qtxs/head-md-future-of-drawing/process/main/2023-12-12/readme.md

# Planning

12.12.2023

Plan for the day

1. Book atelier metal for the first week after vacation
2. Talk with Pierre about project, about 3d print 
3. Prepare for Test Day:

- Read doc again
- Make prototypes
- User scenario
- Better poetry definition
- ...
