qtxs/head-md-future-of-drawing/process/main/2023-12-20/readme.md

# Prototying

In this folder you can find the current version of my assistant, made with two parts.

Things to define:

- final final dimensions
- the small box opening system

I struggle with this two points becase I need my electronics to understand it entirely. All dimensions and sizes in my model are approximativ but very close to reality.

I could find some references for connecting my electronics together:

[!Reference Image](/process/prototyping/2023-12-20/20231912_Connections01.png/)
[!Reference Image](/process/prototyping/2023-12-20/20231912_Connections02.png/)

The entire wiring system shoulb be looking like so:

[!Reference Image](/process/prototyping/2023-12-20/20231912_Wiring.pdf)

Basically in REAL life project, it should be conecting two parts by bluetooth, but for demo I will connect it by cables.

Theses were the sletches:

[!Reference Image](/process/prototyping/2023-12-20/20231912_Sketches01.png)
[!Reference Image](/process/prototyping/2023-12-20/20231912_Sketches02.png)
[!Reference Image](/process/prototyping/2023-12-20/20231912_Sketches03.png)
[!Reference Image](/process/prototyping/2023-12-20/20231912_Sketches04.png)
[!Reference Image](/process/prototyping/2023-12-20/20231912_Sketches05.png)

Yet after discussion with Laure, it came out that this type of object is no more relevant and it requires major changes. (see next day)
