qtxs/head-md-future-of-drawing/process/main/2023-10-30/20231030_Prototype_01.2.JPG

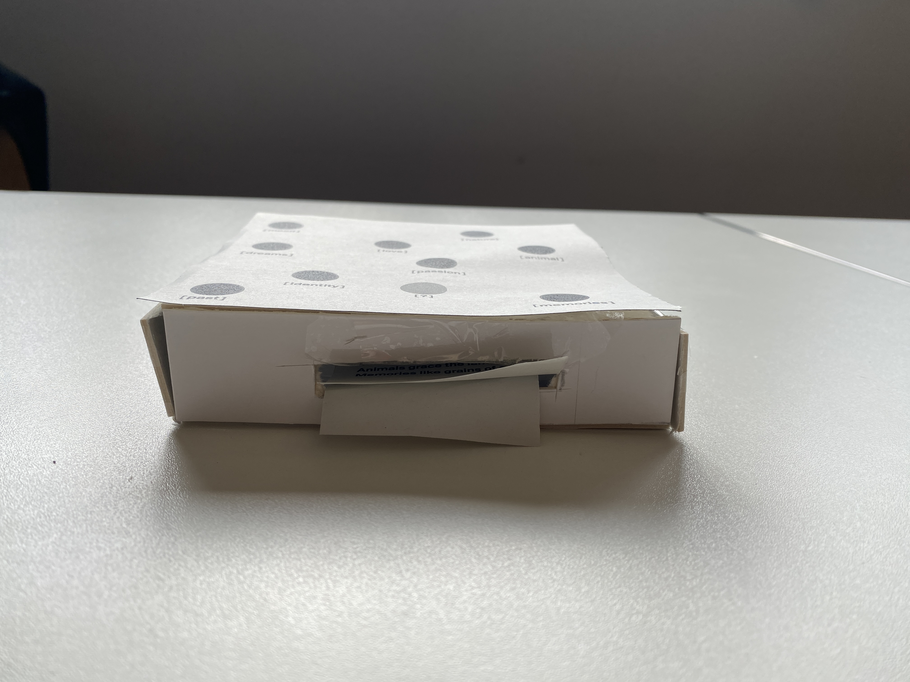
process/main/2023-10-30/20231030_Prototype_01.2.JPG
