qtxs/head-md-future-of-drawing/process/main/2023-11-02/20231103_Idea02_User_Journey.png

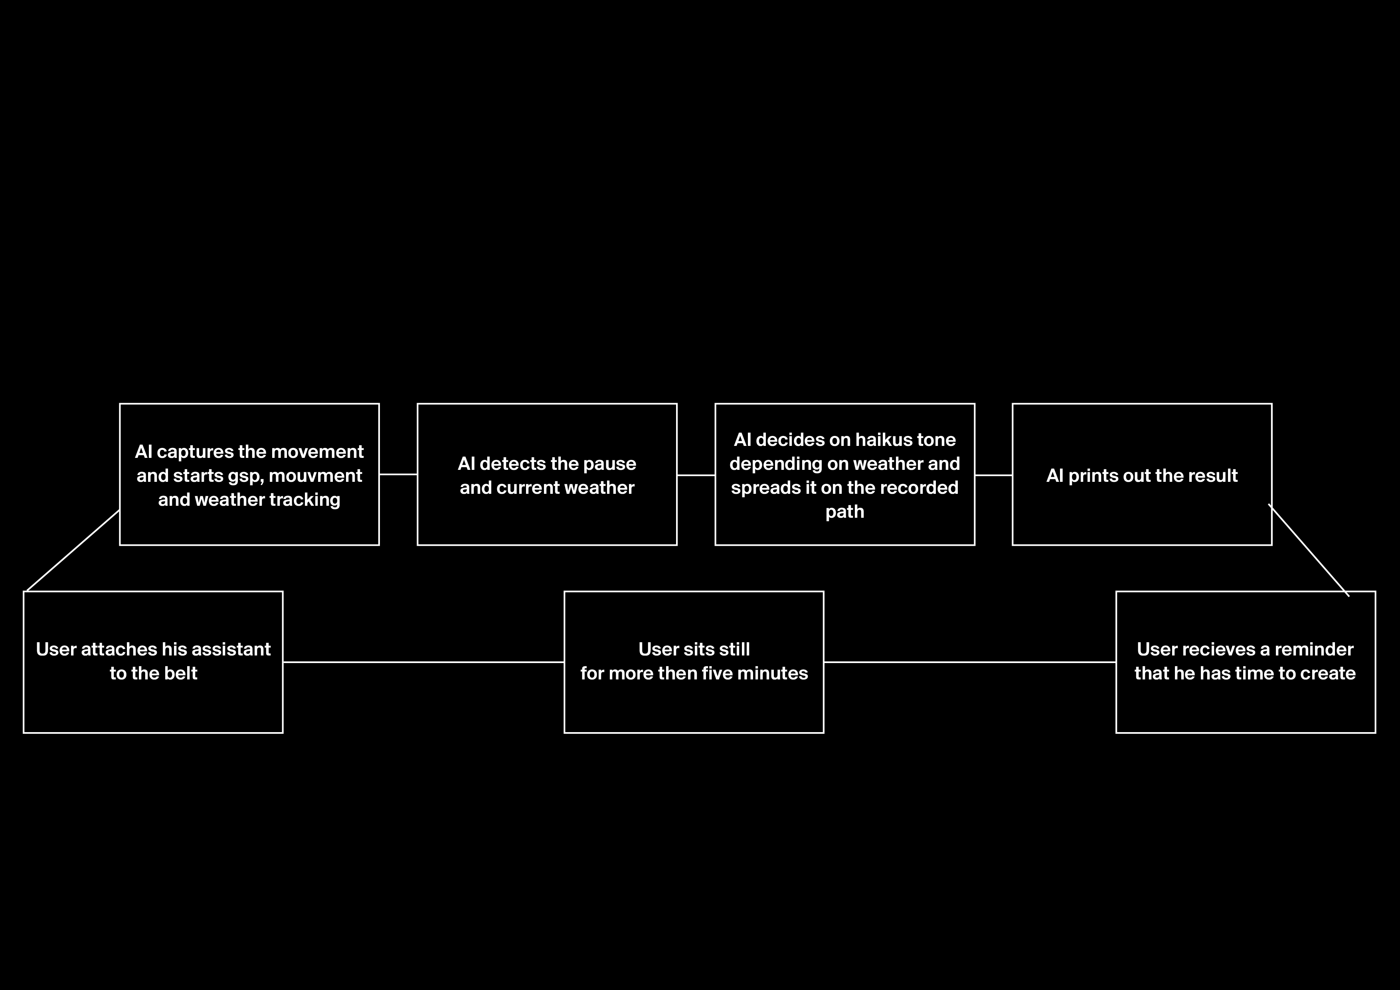
process/main/2023-11-02/20231103_Idea02_User_Journey.png
