qtxs/head-md-future-of-drawing/process/main/2023-11-16/20231116_MyBox02.png

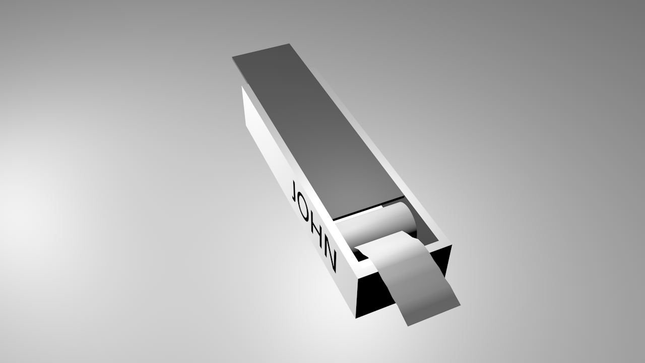
process/main/2023-11-16/20231116_MyBox02.png
