qtxs/head-md-future-of-drawing/process/main/2023-11-16/20231116_RefBox03.png

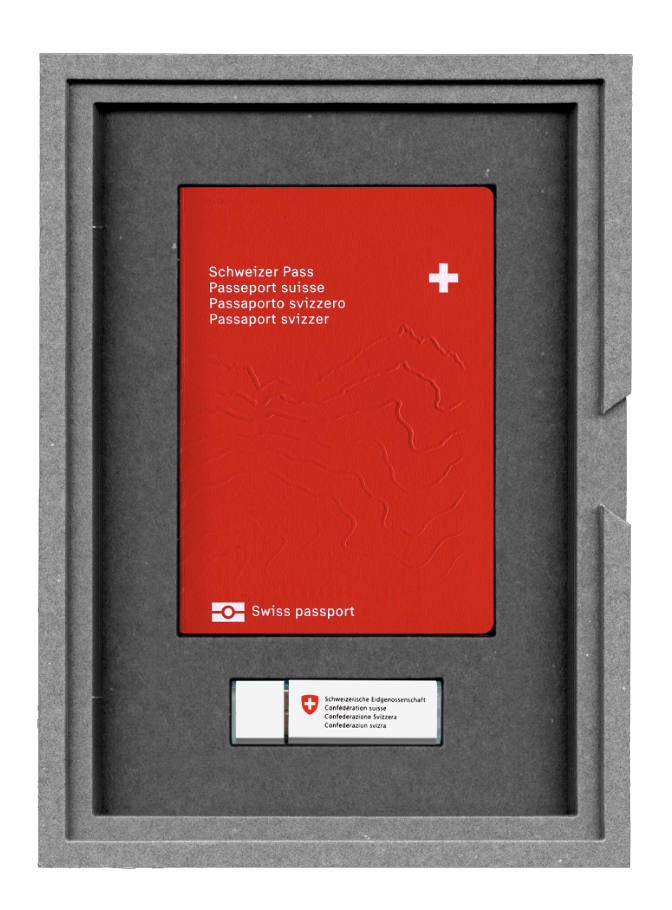
process/main/2023-11-16/20231116_RefBox03.png
