qtxs/head-md-future-of-drawing/process/main/2023-11-23/20231121_Ref01.jpeg

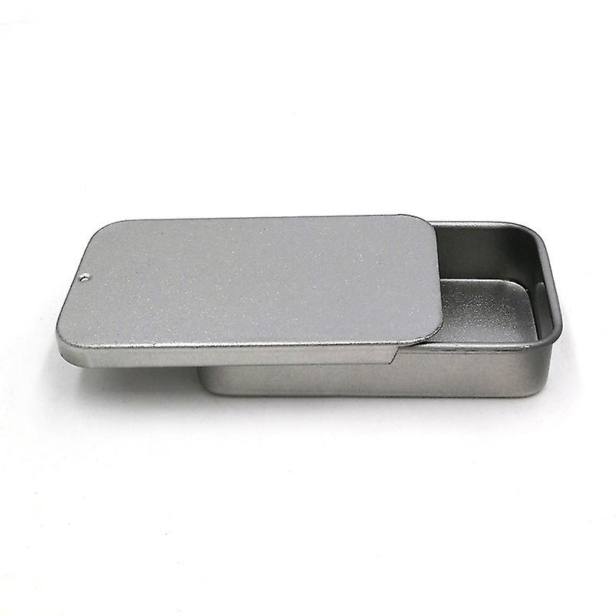
process/main/2023-11-23/20231121_Ref01.jpeg
