qtxs/head-md-future-of-drawing/process/main/2023-12-04/20231204_Ref02.png

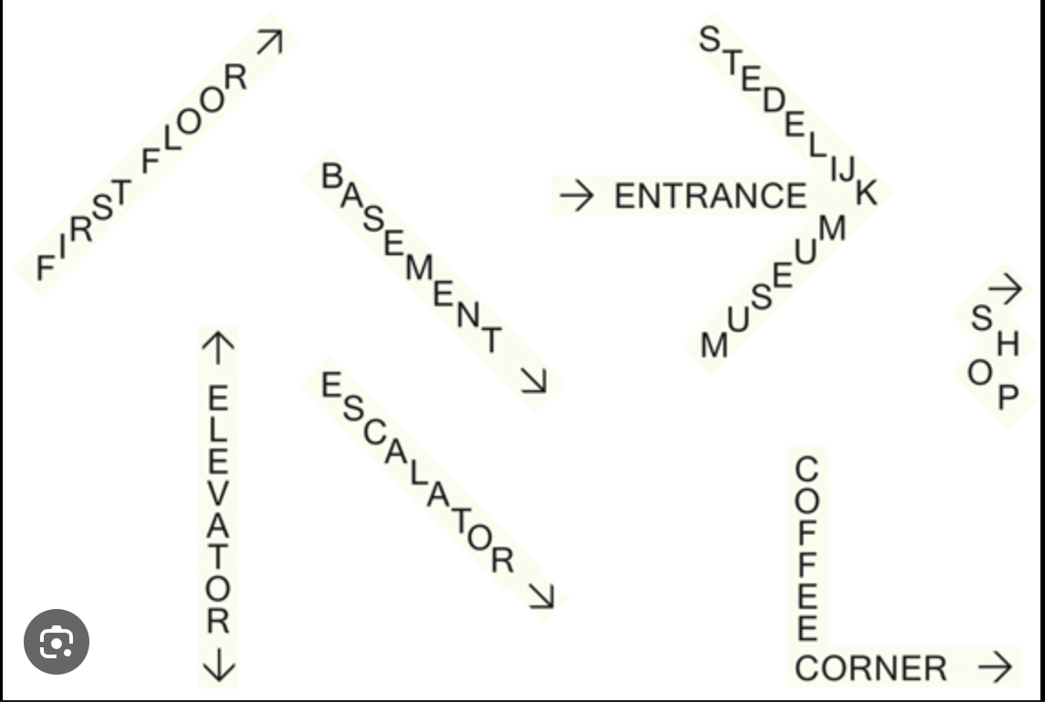
process/main/2023-12-04/20231204_Ref02.png
