qtxs/head-md-future-of-drawing/process/main/2023-12-08/20231208_Boxes2.png

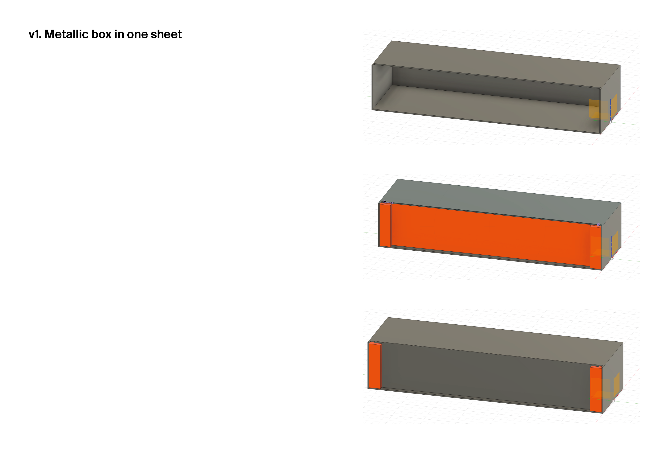
process/main/2023-12-08/20231208_Boxes2.png
