qtxs/head-md-future-of-drawing/process/main/2023-12-20/20231912_Sketches03.png

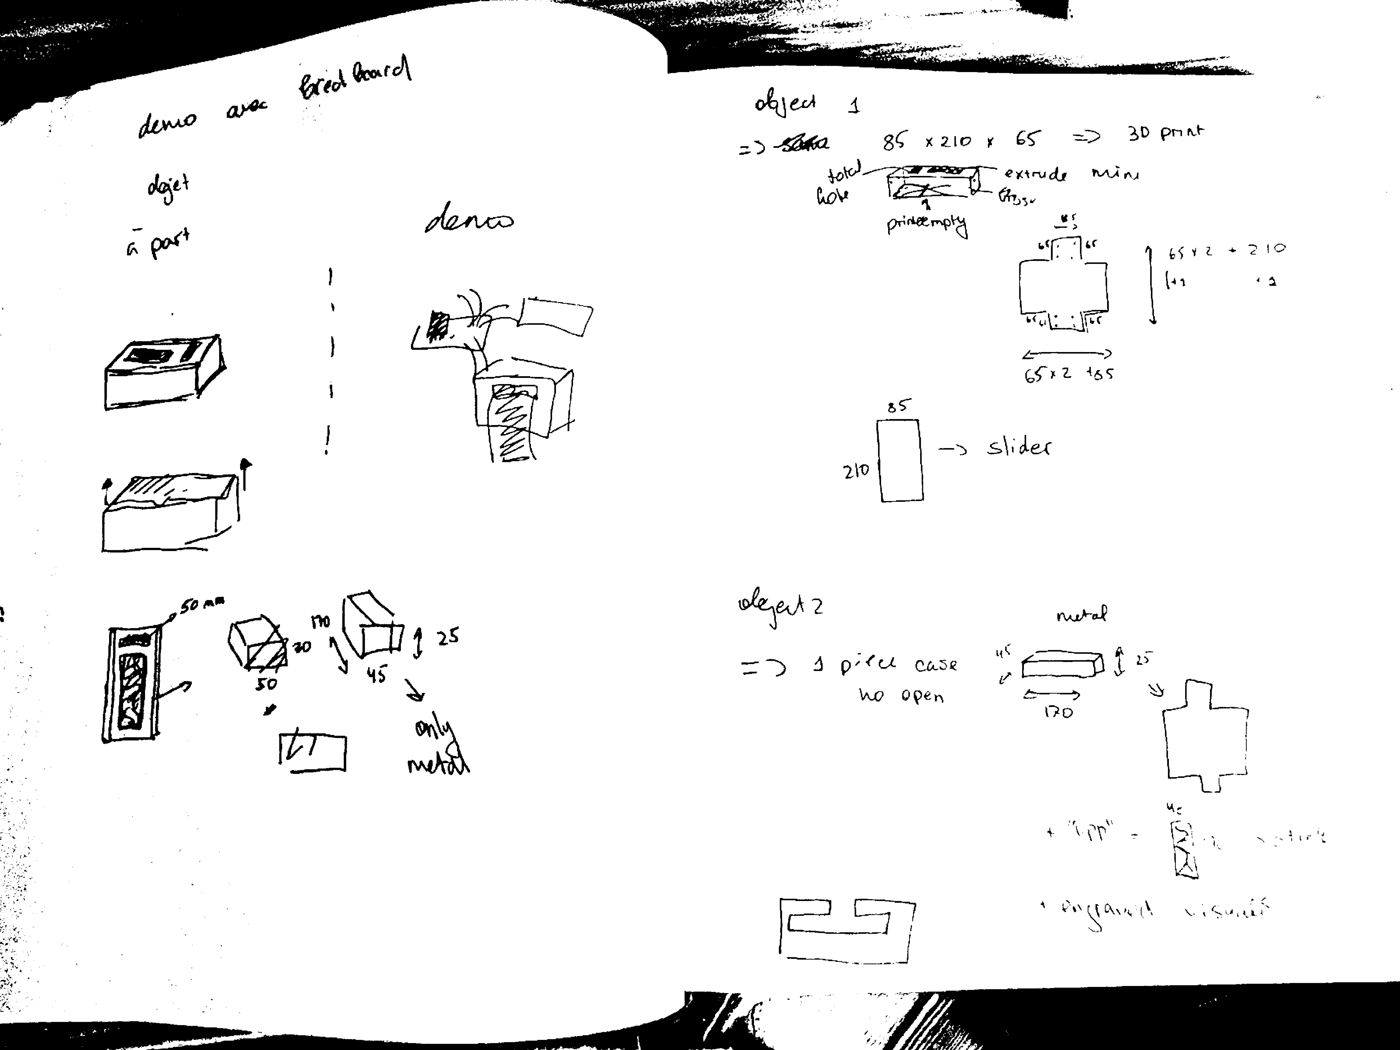
process/main/2023-12-20/20231912_Sketches03.png
