qtxs/head-md-future-of-drawing/process/main/2023-12-21/20231221_NewRefs/image (5).png

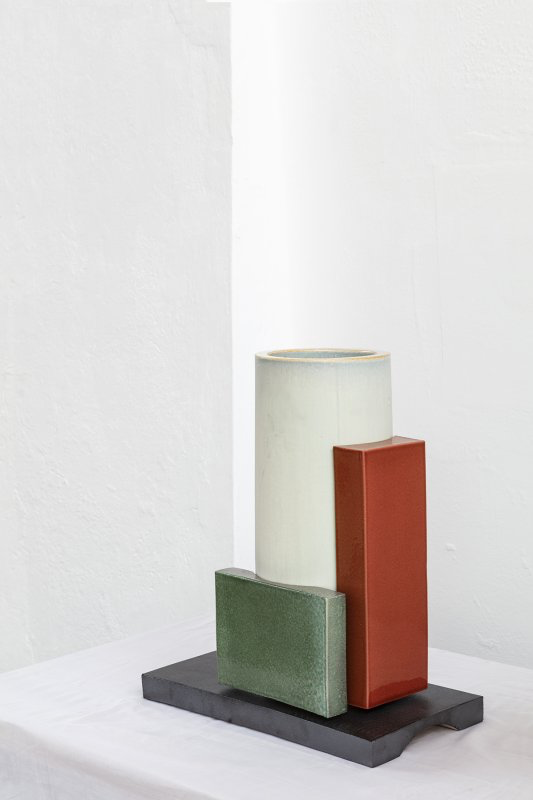
process/main/2023-12-21/20231221_NewRefs/image (5).png
