qtxs/head-md-future-of-drawing/process/main/2023-12-21/20231221_NewRefs/Screenshot 2023-12-21 at 11.53.56.png

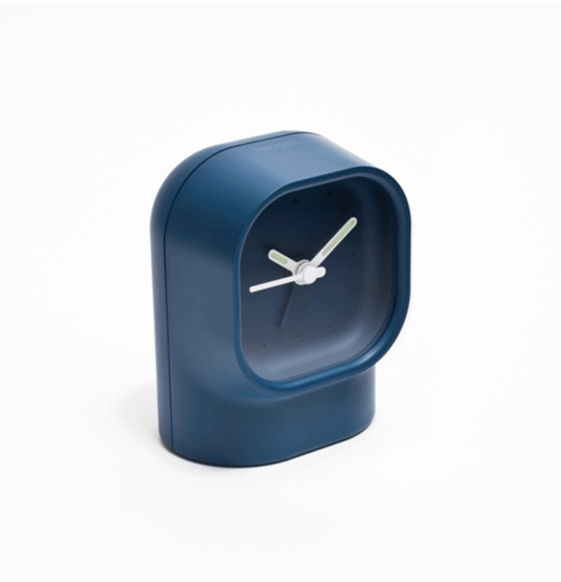
process/main/2023-12-21/20231221_NewRefs/Screenshot 2023-12-21 at 11.53.56.png
