qtxs/head-md-future-of-drawing/process/main/2023-12-29/20231229_Scheme02.png

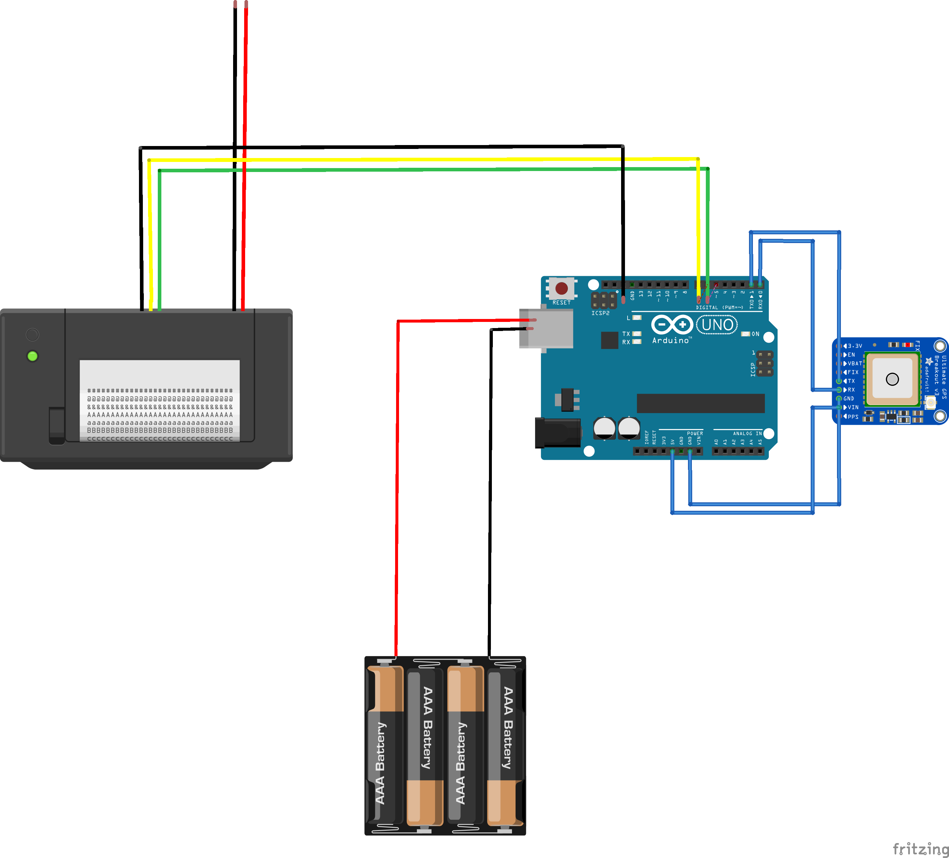
process/main/2023-12-29/20231229_Scheme02.png
