qtxs/head-md-future-of-drawing/process/main/2023-12-29/IMG_7831.JPG

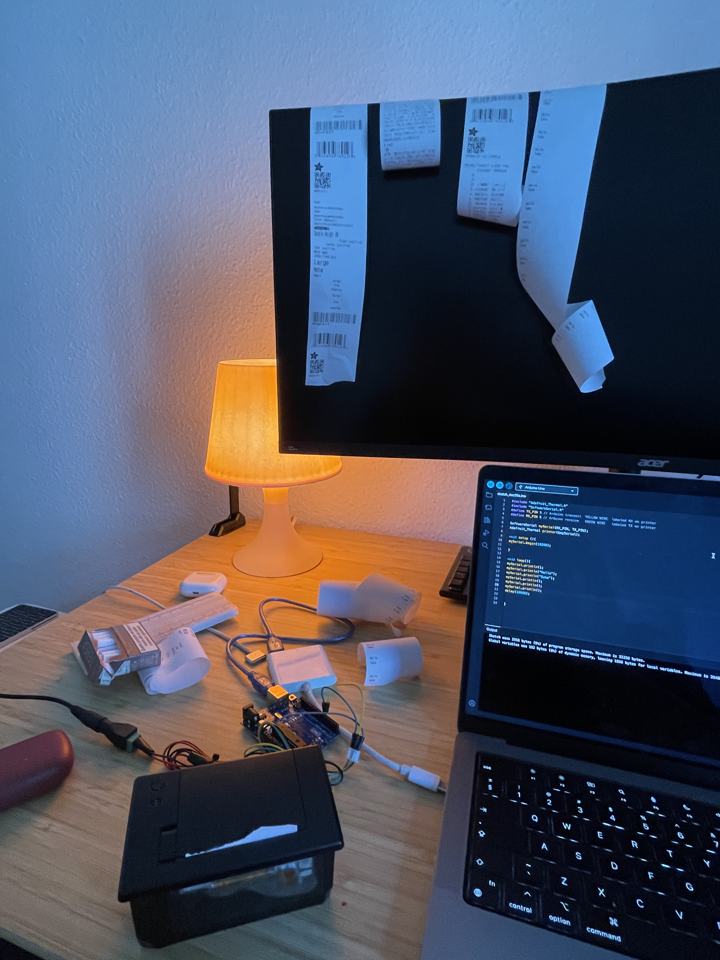
process/main/2023-12-29/IMG_7831.JPG
