qtxs/head-md-future-of-drawing/process/main/2024-01-05/Screenshot 2024-01-05 at 10.59.29.png

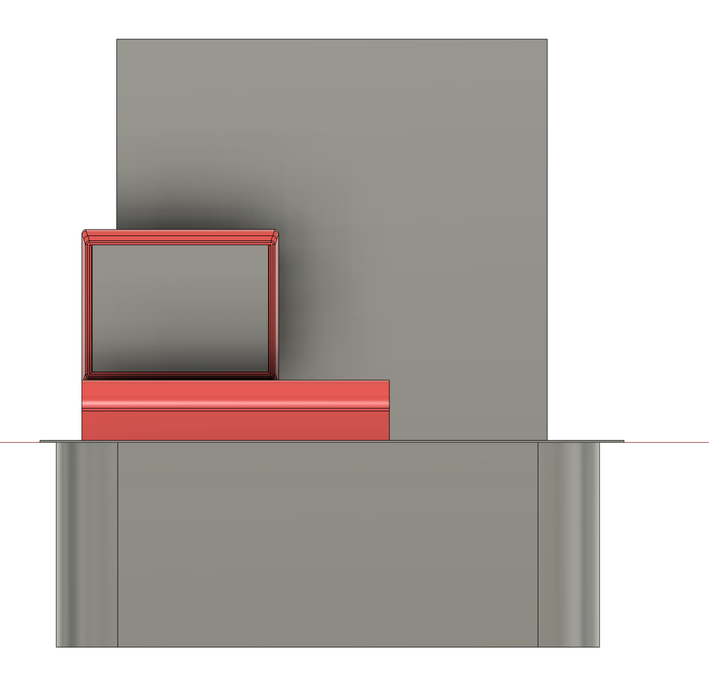
process/main/2024-01-05/Screenshot 2024-01-05 at 10.59.29.png
