qtxs/head-md-future-of-drawing/process/main/2024-01-10/20241210_Him.JPG

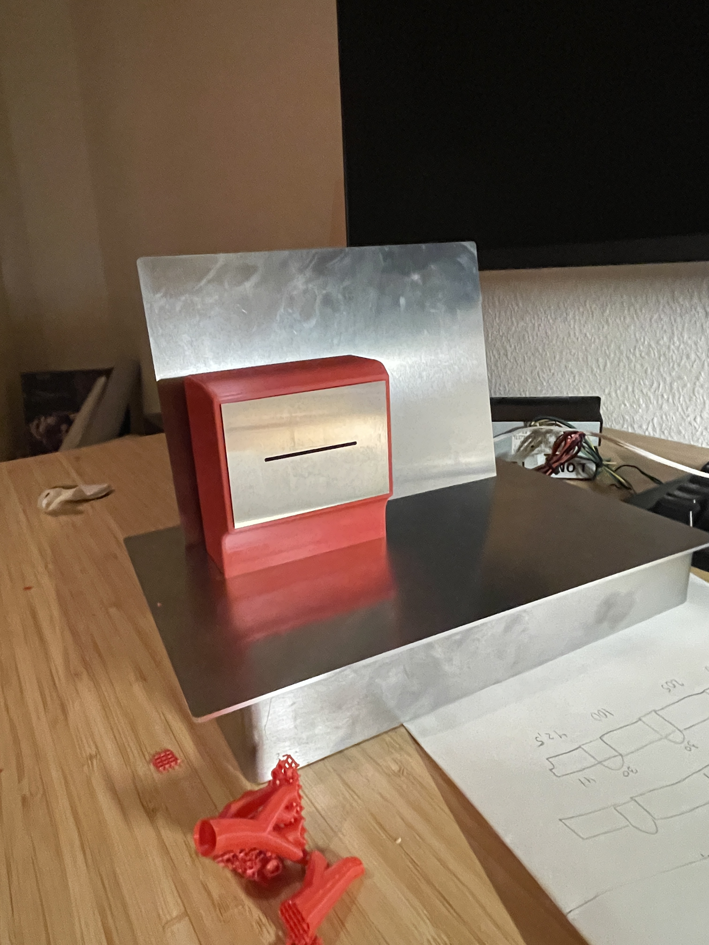
process/main/2024-01-10/20241210_Him.JPG
