qtxs/head-md-future-of-drawing/process/main/2024-01-10/20241210_ShapeNew.png

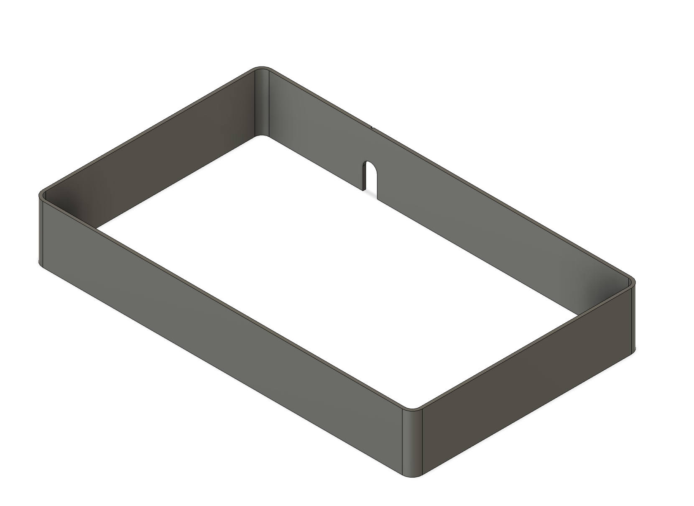
process/main/2024-01-10/20241210_ShapeNew.png
