qtxs/head-md-future-of-drawing/process/main/2024-01-10/20241210_Supports1.png

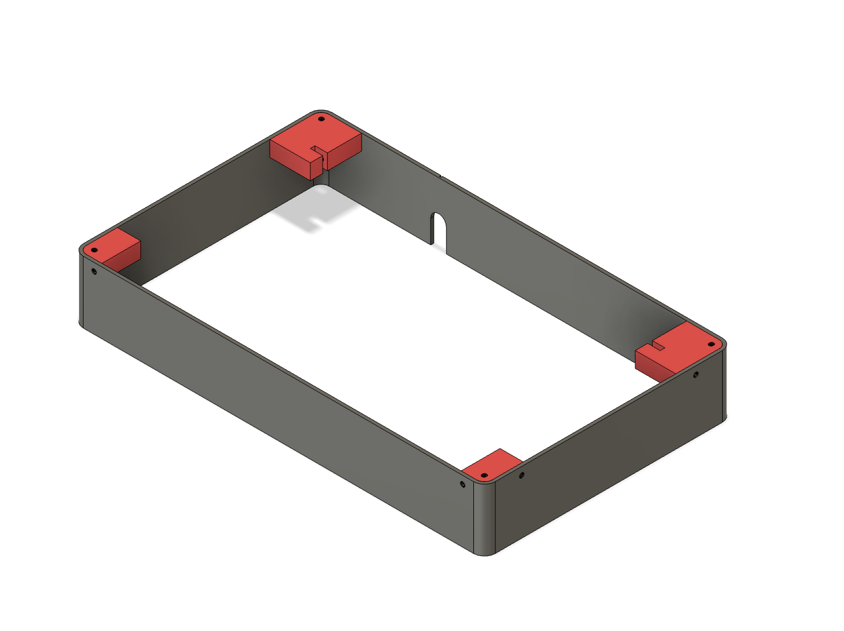
process/main/2024-01-10/20241210_Supports1.png
