qtxs/head-md-future-of-drawing/process/main/2024-01-12/20241212_Portable.png

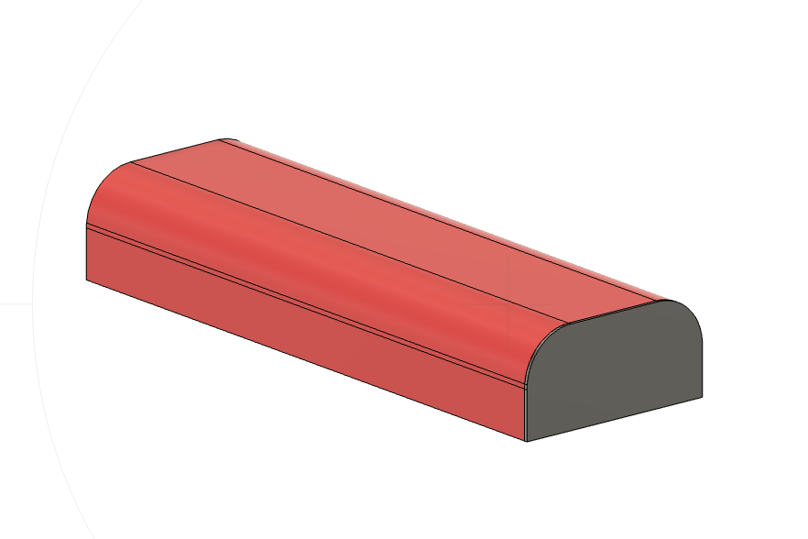
process/main/2024-01-12/20241212_Portable.png
