qtxs/head-md-future-of-drawing/process/main/2024-01-13/20240113_Solution0.png

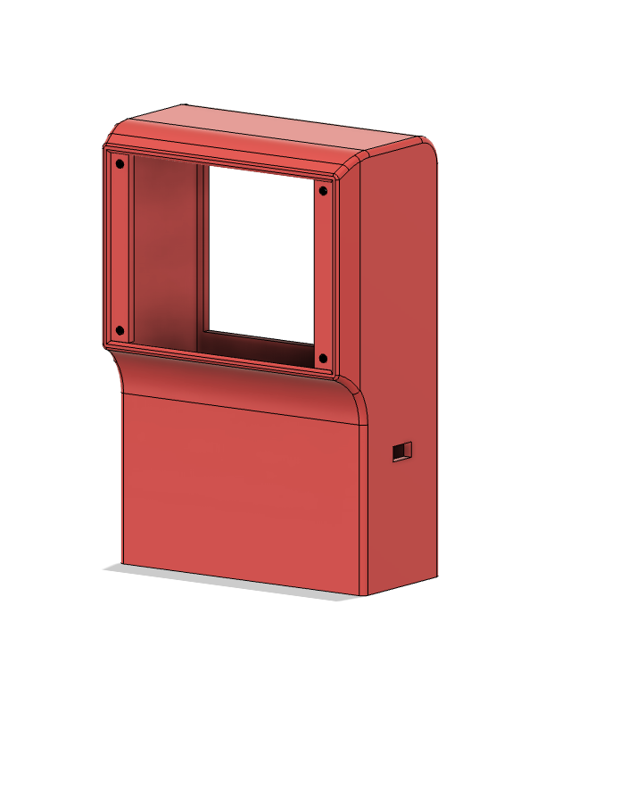
process/main/2024-01-13/20240113_Solution0.png
