qtxs/head-md-future-of-drawing/process/main/2024-01-15/Bitmaps/poems/poems4.png

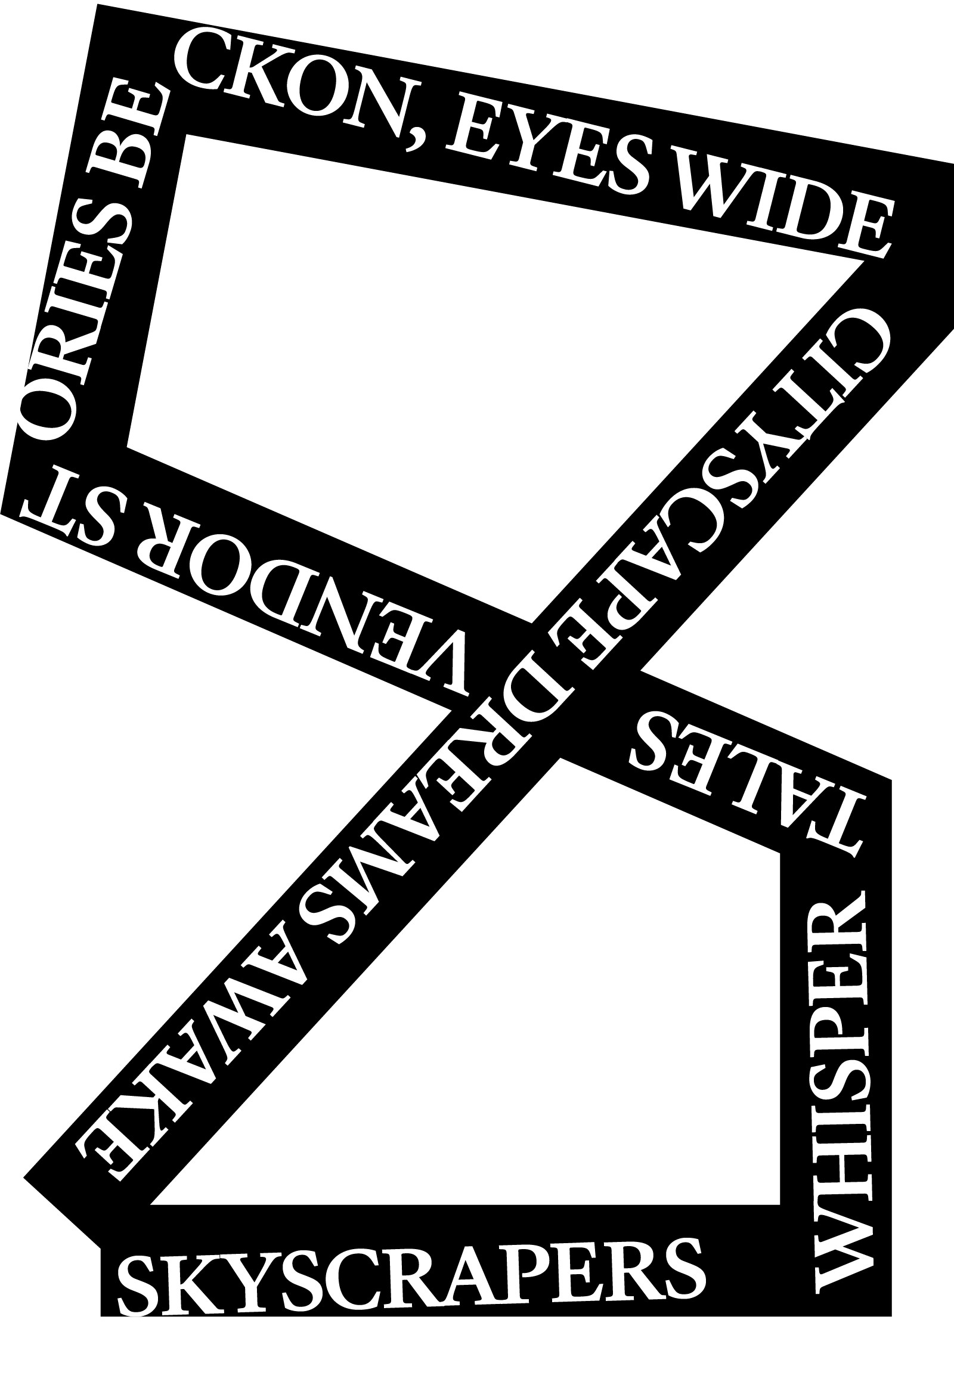
process/main/2024-01-15/Bitmaps/poems/poems4.png
