qtxs/head-md-future-of-drawing/process/main/2024-01-15/Bitmaps/scans/scan_ekaterin.bliznyuk_2024-01-15-14-48-56_1.jpeg

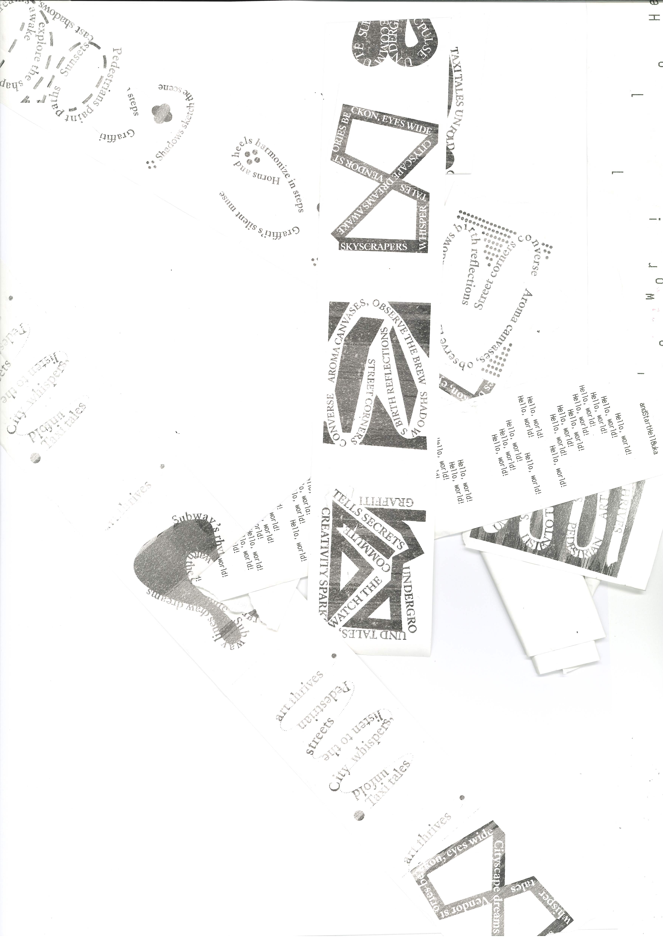
process/main/2024-01-15/Bitmaps/scans/scan_ekaterin.bliznyuk_2024-01-15-14-48-56_1.jpeg
