qtxs/head-md-future-of-drawing/process/main/2024-01-15/front01.png

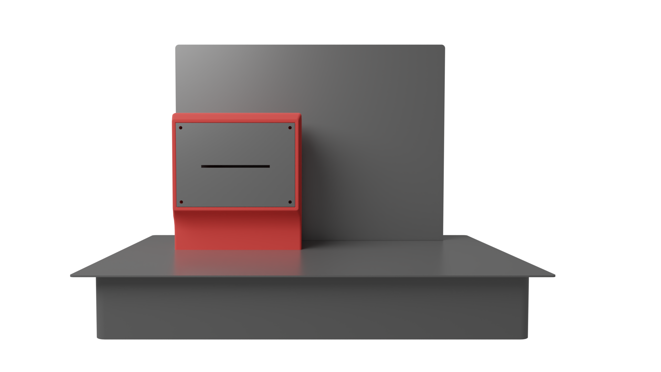
process/main/2024-01-15/front01.png
