qtxs/head-md-future-of-drawing/process/main/2024-01-16/20240116_CoverFront.png

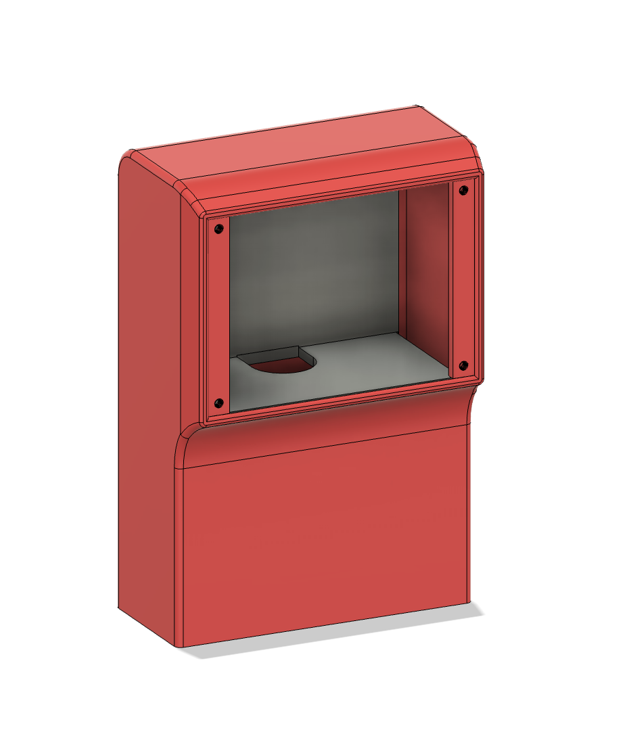
process/main/2024-01-16/20240116_CoverFront.png
