qtxs/head-md-future-of-drawing/process/main/2024-01-16/20240116_Nerding.JPG

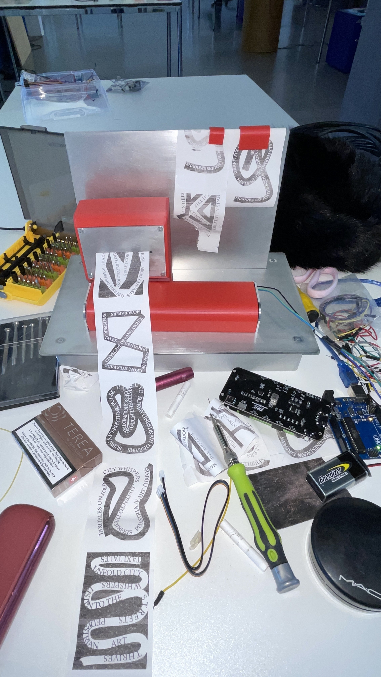
process/main/2024-01-16/20240116_Nerding.JPG
