qtxs/head-md-future-of-drawing/process/presentations/pres pics/IMG_7099.PNG

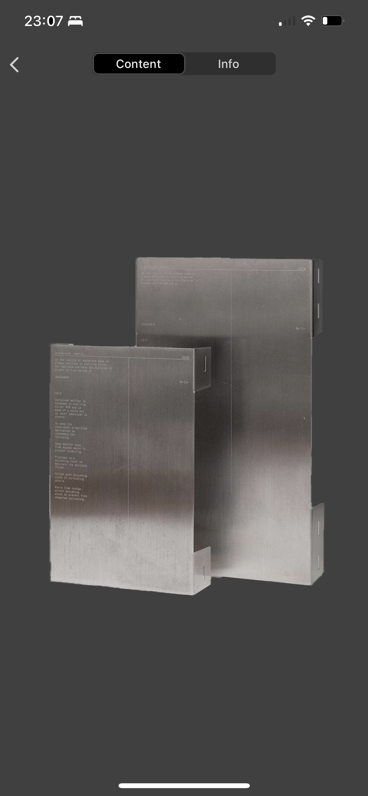
process/presentations/pres pics/IMG_7099.PNG
