qtxs/head-md-future-of-drawing/process/presentations/pres pics/IMG_7113.JPG

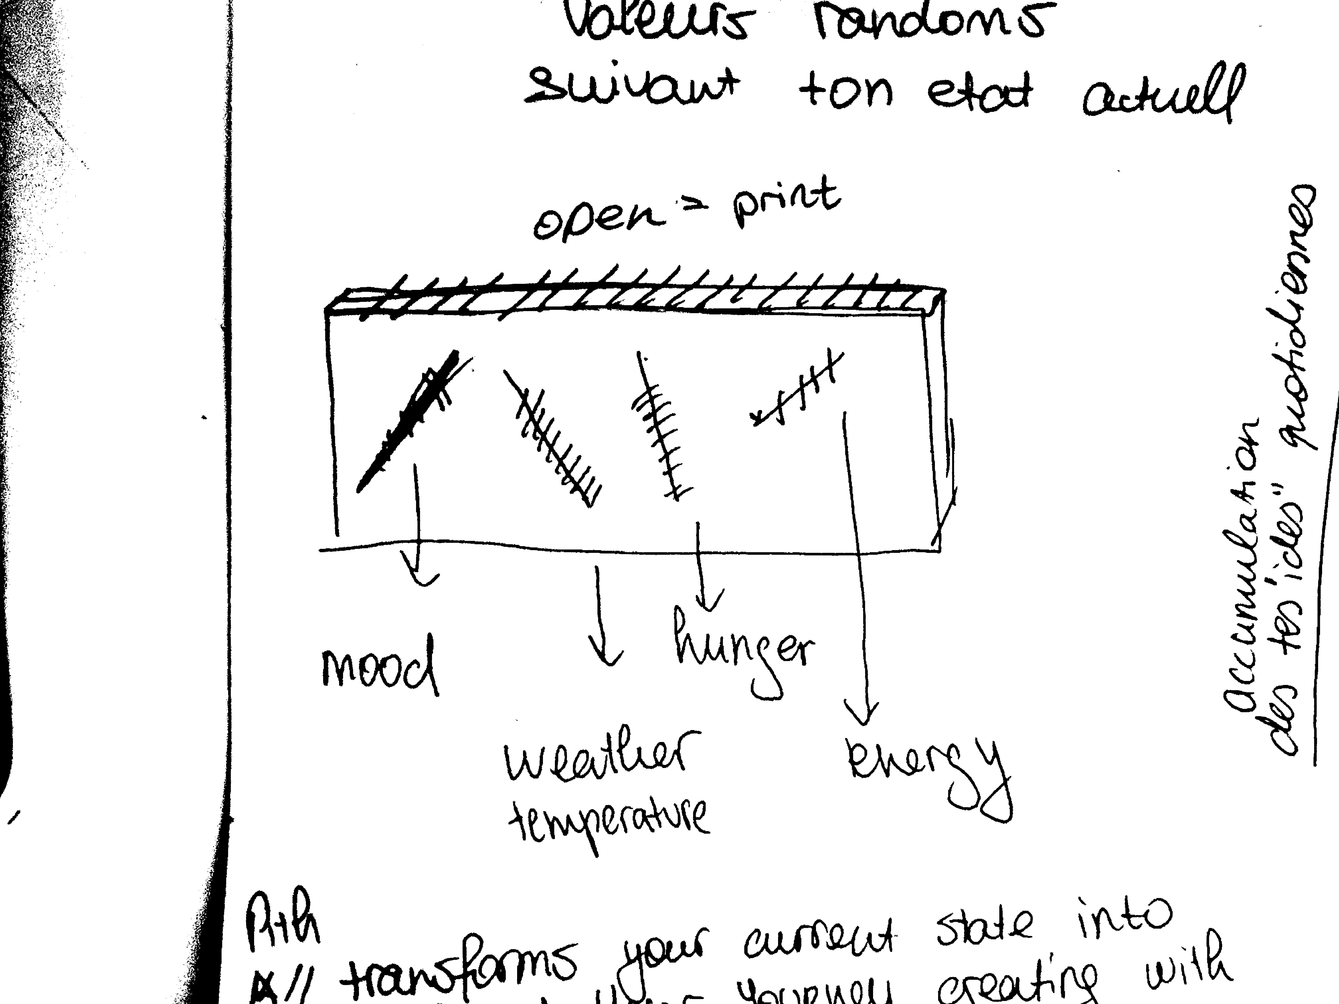
process/presentations/pres pics/IMG_7113.JPG
