qtxs/head-md-future-of-drawing/process/presentations/pres pics/IMG_7124.JPG

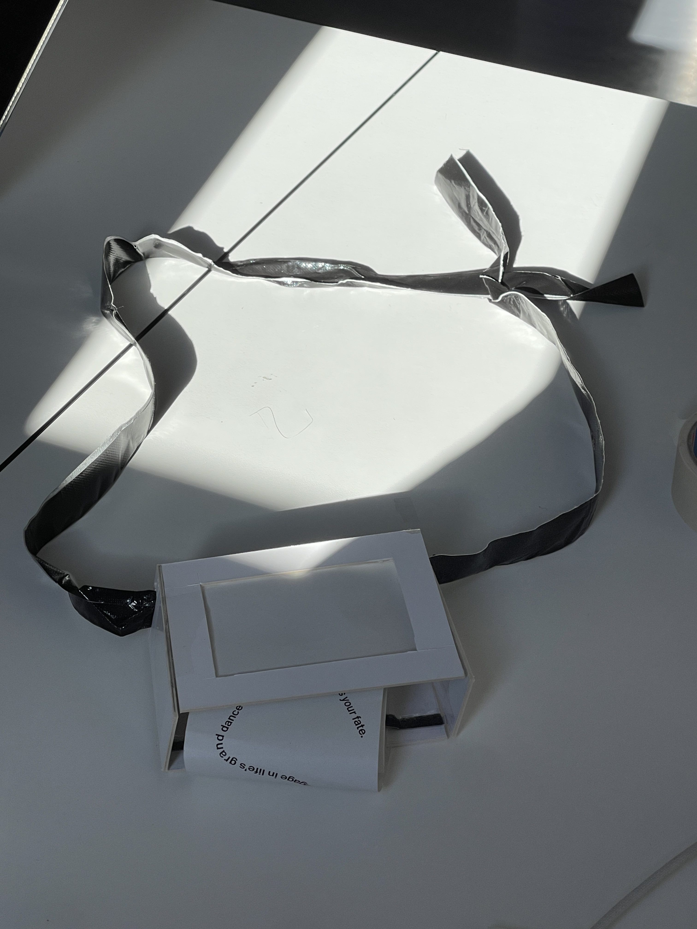
process/presentations/pres pics/IMG_7124.JPG
