qtxs/head-md-future-of-drawing/process/presentations/pres pics/IMG_7129.JPG

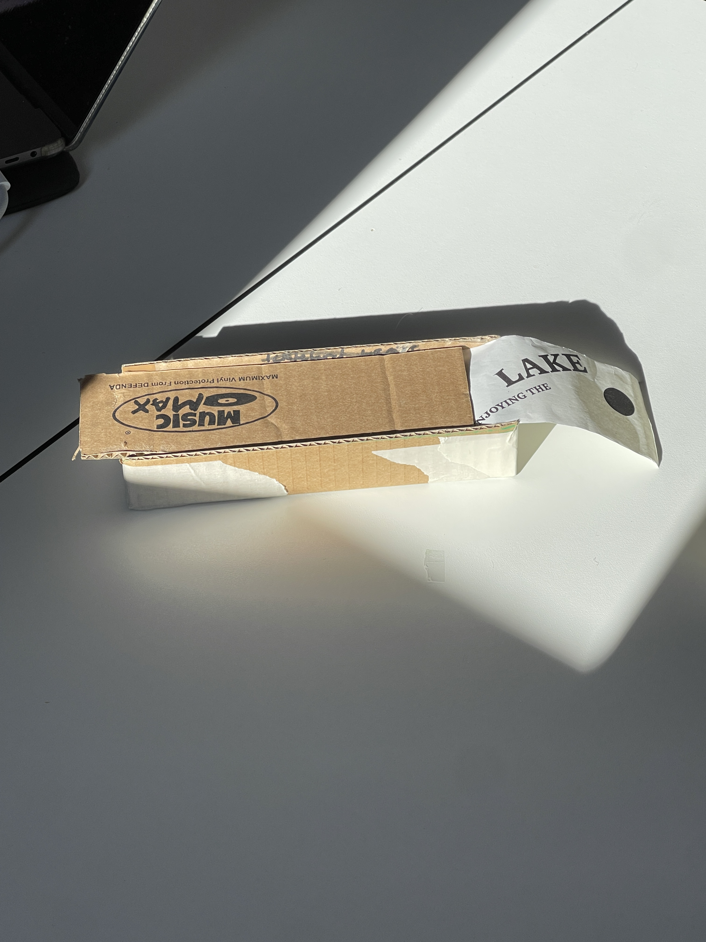
process/presentations/pres pics/IMG_7129.JPG
