qtxs/head-md-future-of-drawing/process/presentations/pres pics/IMG_7136.JPG

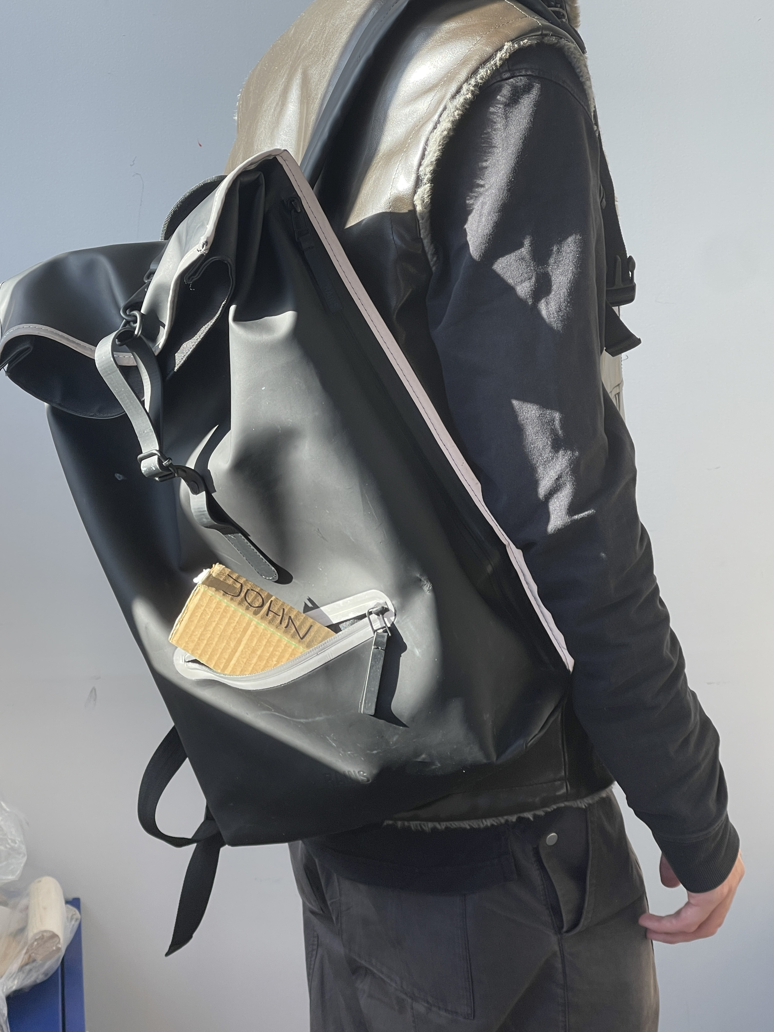
process/presentations/pres pics/IMG_7136.JPG
