qtxs/head-md-future-of-drawing/process/presentations/pres pics/IMG_7146.JPG

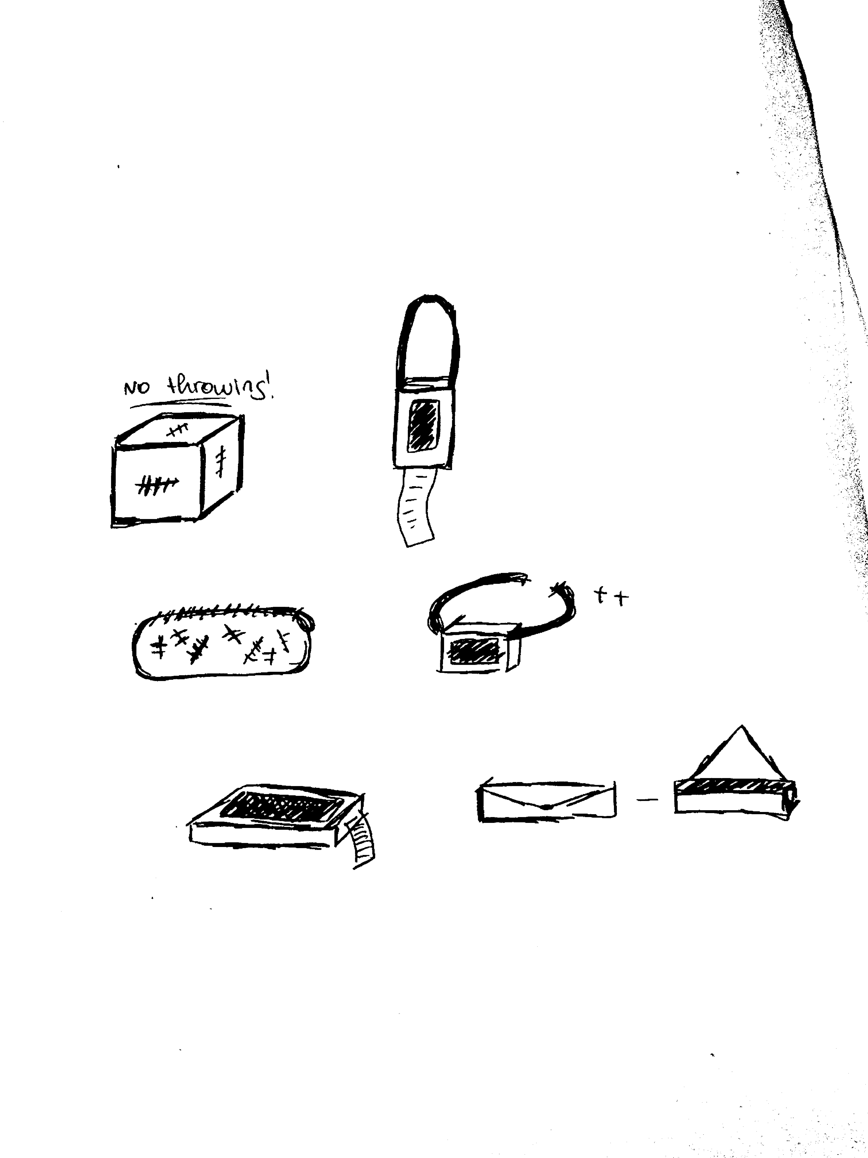
process/presentations/pres pics/IMG_7146.JPG
