qtxs/head-md-future-of-drawing/process/random-notes/IMG_6725.PNG

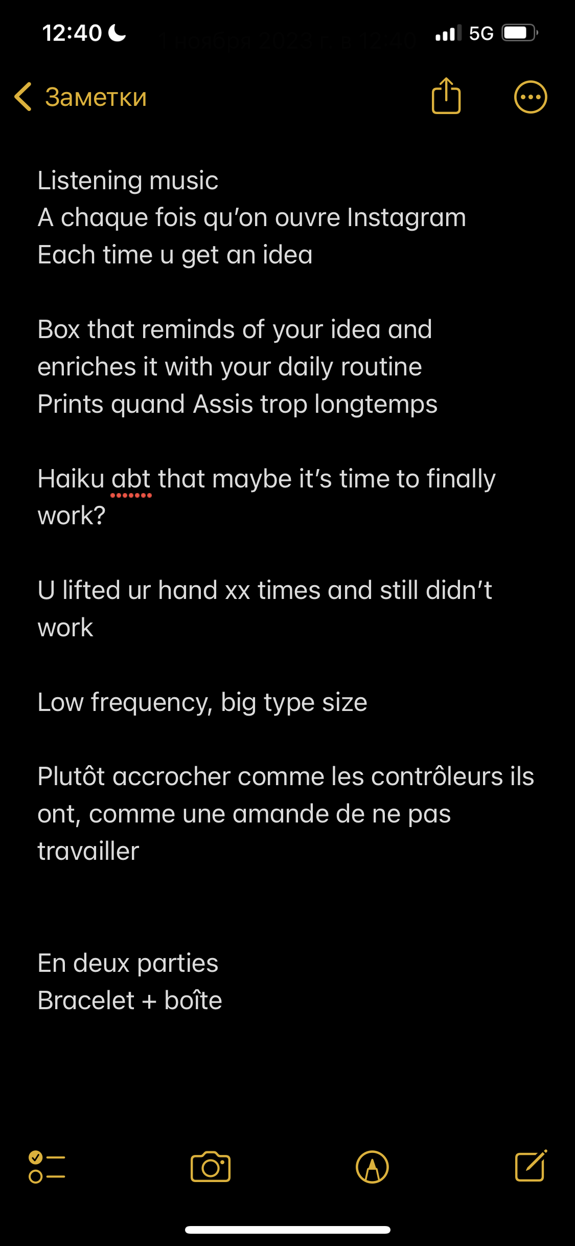
process/random-notes/IMG_6725.PNG
