qtxs/head-md-future-of-drawing/process/random-notes/IMG_6726.PNG

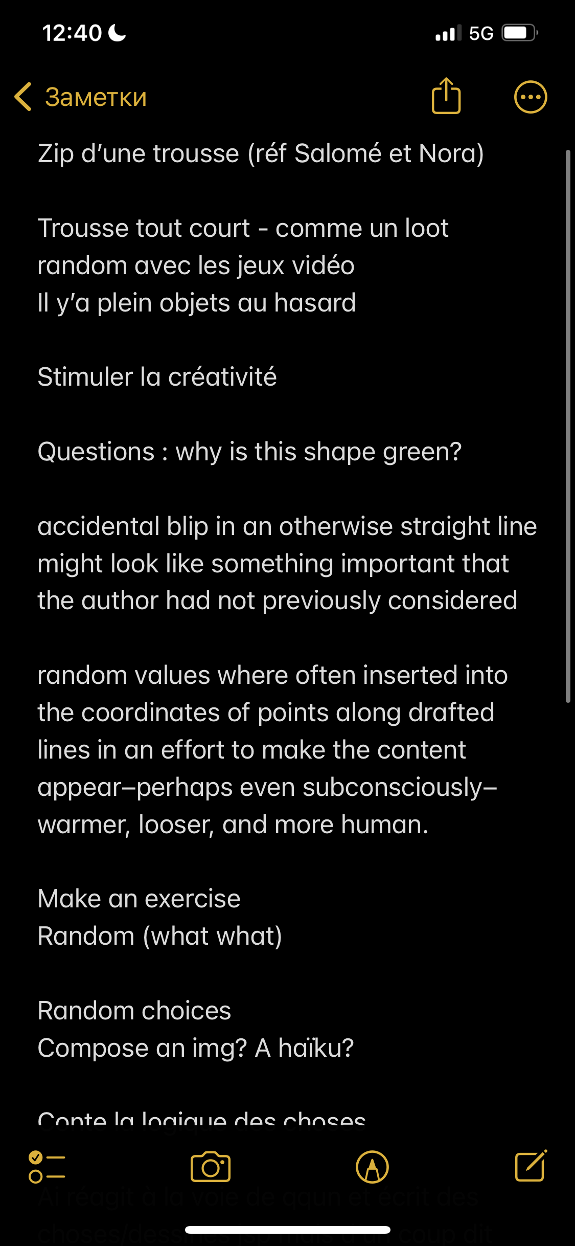
process/random-notes/IMG_6726.PNG
