qtxs/head-md-future-of-drawing/process/random-notes/IMG_6727.jpg

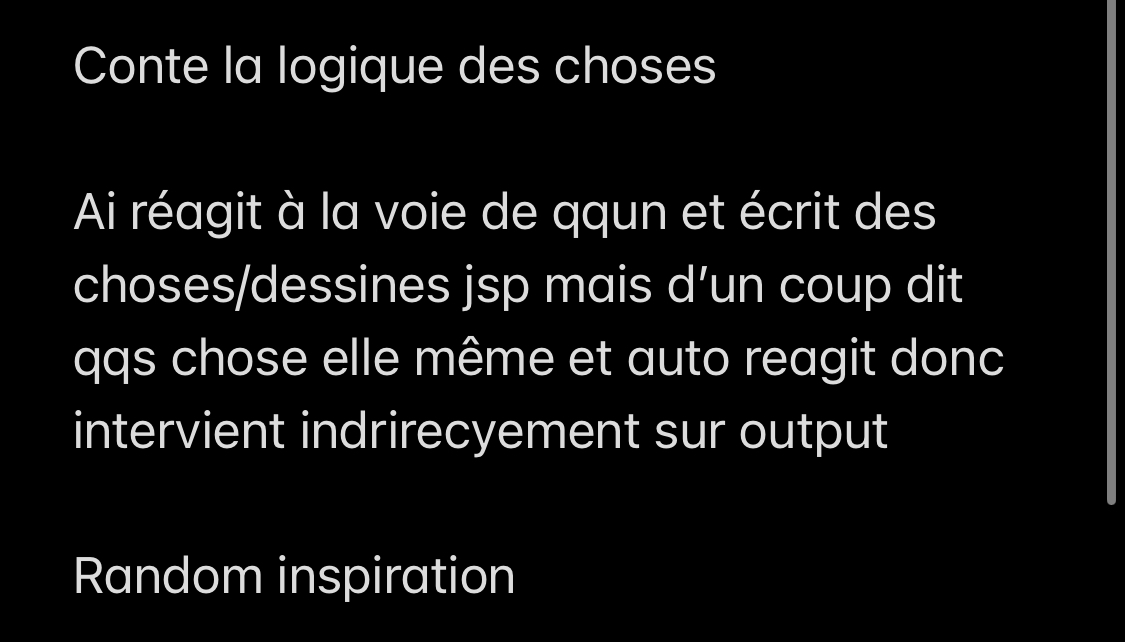
process/random-notes/IMG_6727.jpg
