qtxs/head-md-future-of-drawing/process/random-notes/IMG_6728.PNG

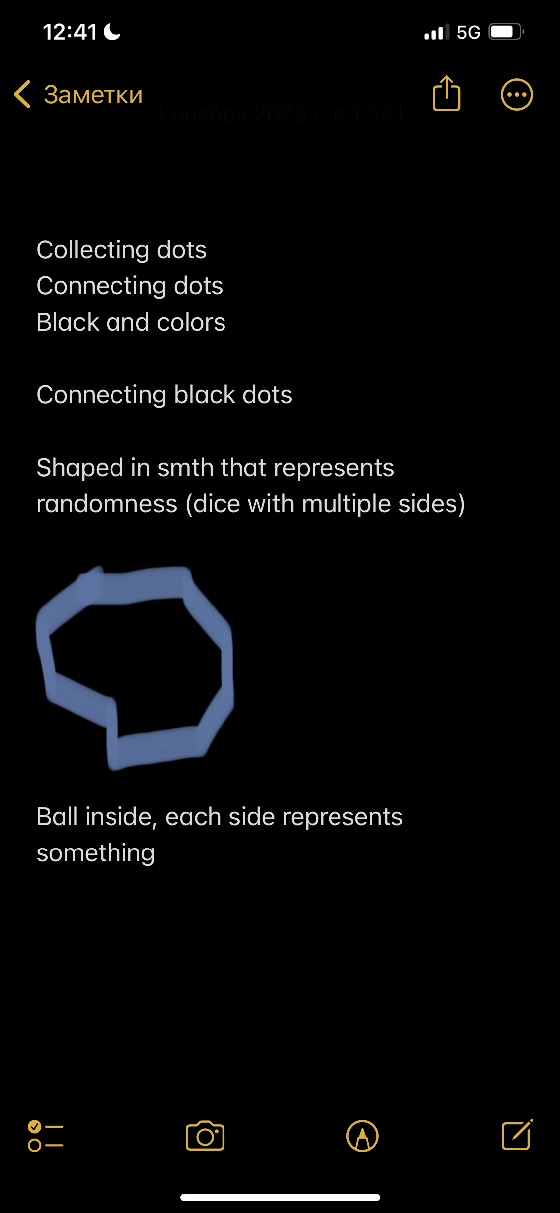
process/random-notes/IMG_6728.PNG
