qtxs/head-md-future-of-drawing/process/random-notes/IMG_6729.PNG

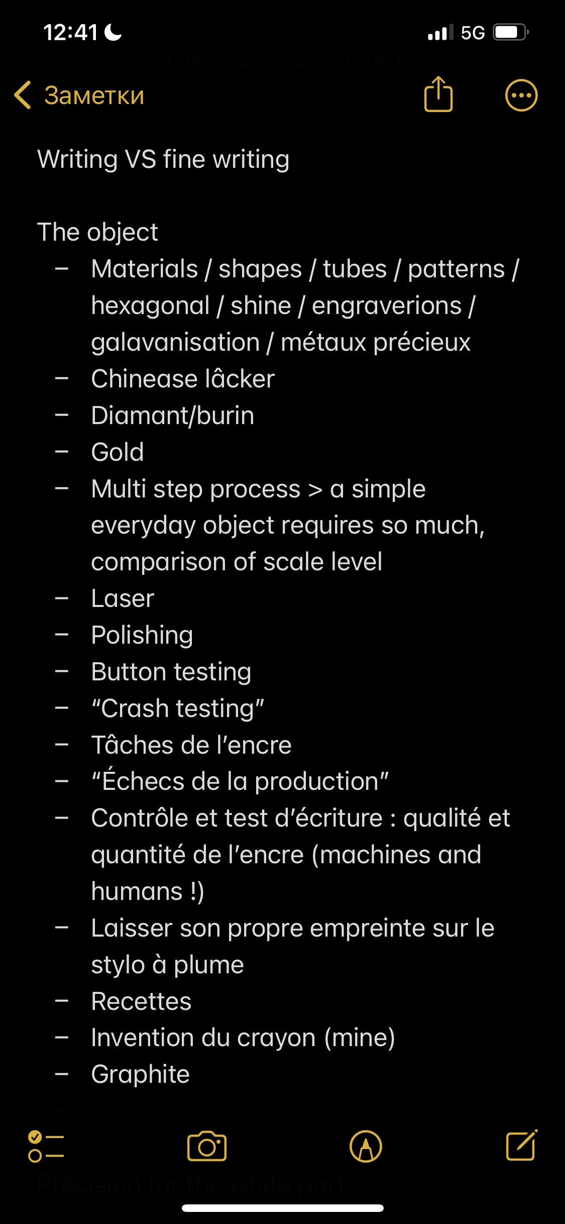
process/random-notes/IMG_6729.PNG
