qtxs/head-md-future-of-drawing/process/references/1_ff004001cd1d47d2aa74b2b5f81daacf-683x1024.jpg

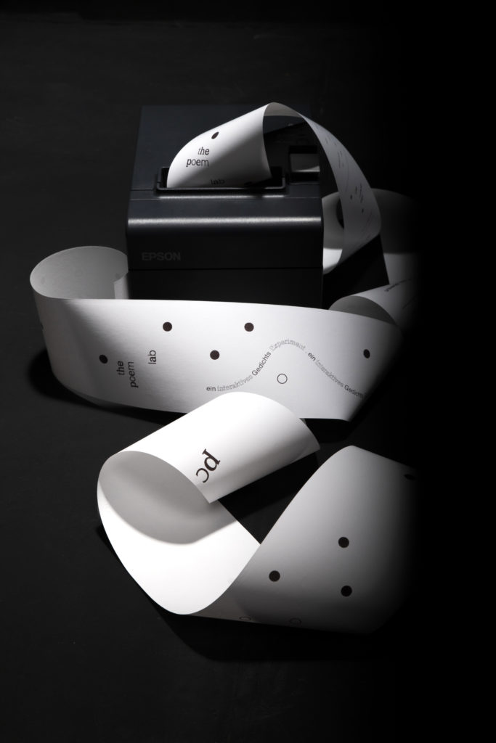
process/references/1_ff004001cd1d47d2aa74b2b5f81daacf-683x1024.jpg
