qtxs/head-md-future-of-drawing/process/references/3_51cdbd26519a4e77a11e635c95dcc360-1024x522.jpg

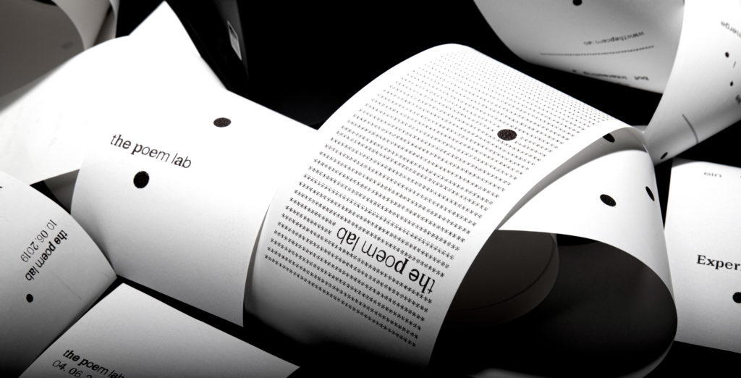
process/references/3_51cdbd26519a4e77a11e635c95dcc360-1024x522.jpg
