qtxs/head-md-future-of-drawing/process/references/0103c9cd1fa8e9f3f9c3bbae9f55c347.jpg

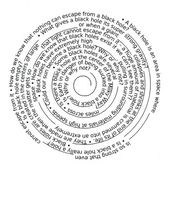
process/references/0103c9cd1fa8e9f3f9c3bbae9f55c347.jpg
