qtxs/head-md-future-of-drawing/process/references/360_F_97092981_Kblzv0GnkSNFeFCzhQ8Ded1qef5isQM3.jpg

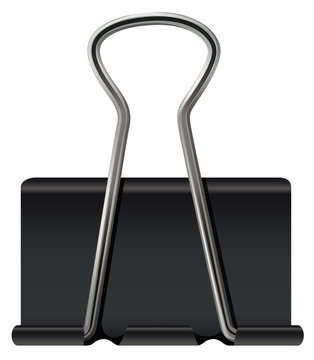
process/references/360_F_97092981_Kblzv0GnkSNFeFCzhQ8Ded1qef5isQM3.jpg
