qtxs/head-md-future-of-drawing/process/references/421dc679068945.5cb781c352a6e.jpg

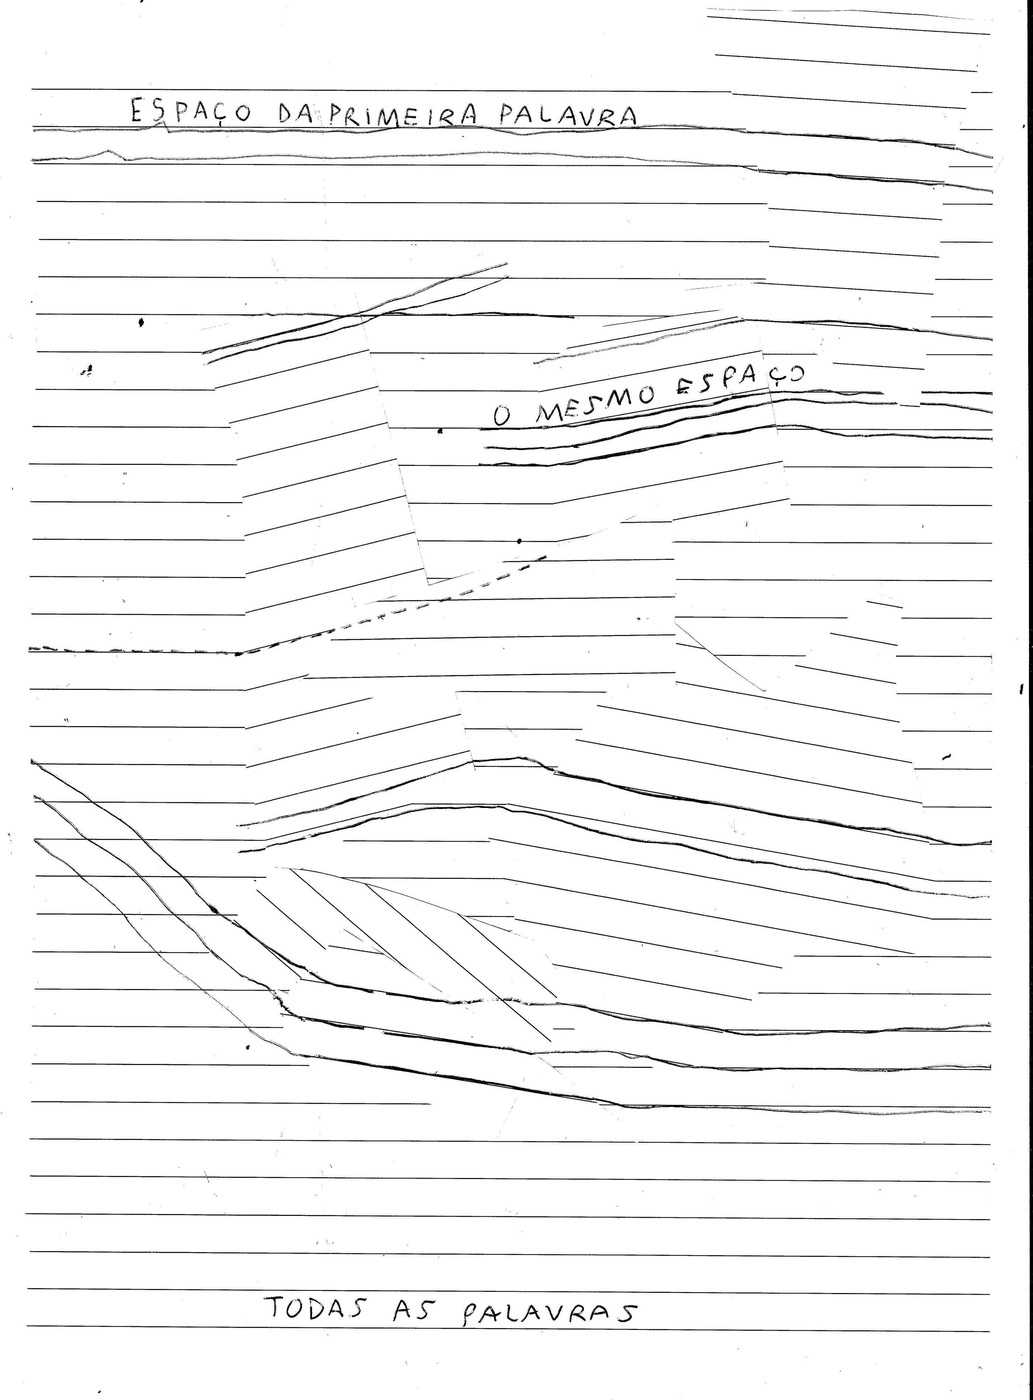
process/references/421dc679068945.5cb781c352a6e.jpg
