qtxs/head-md-future-of-drawing/process/references/968d51177812303.64dd09c569897.jpg

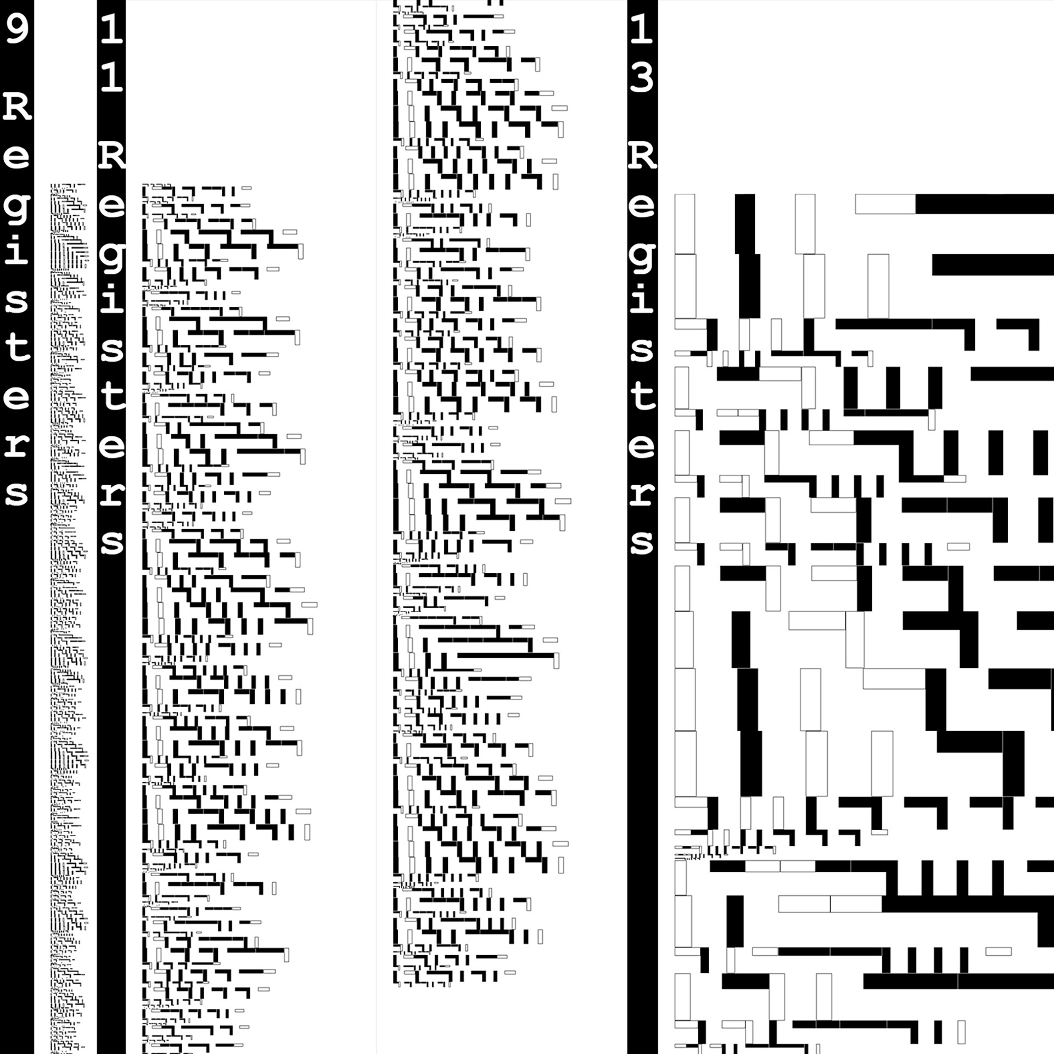
process/references/968d51177812303.64dd09c569897.jpg
