qtxs/head-md-future-of-drawing/process/references/20231116_RefBox01.png

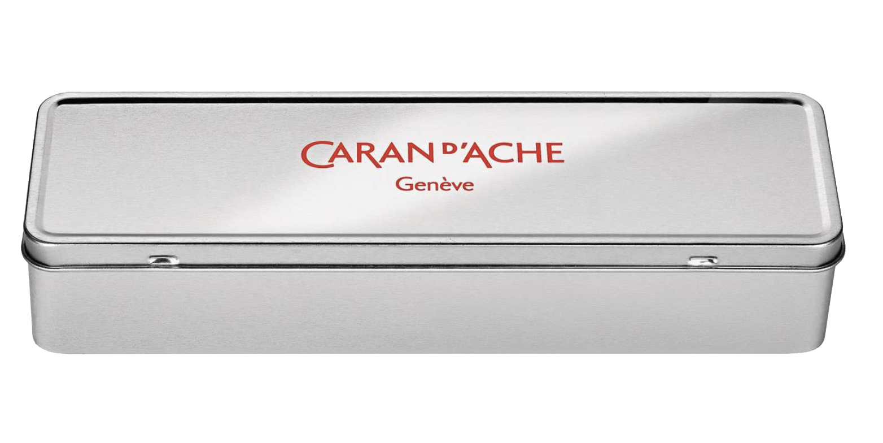
process/references/20231116_RefBox01.png
