qtxs/head-md-future-of-drawing/process/references/20231116_RefBox02.png

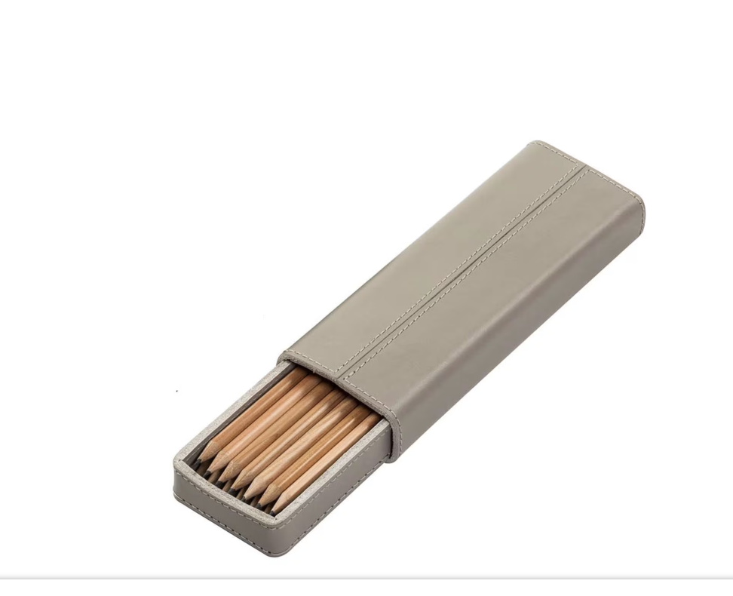
process/references/20231116_RefBox02.png
