qtxs/head-md-future-of-drawing/process/references/20231116_RefBox03.png

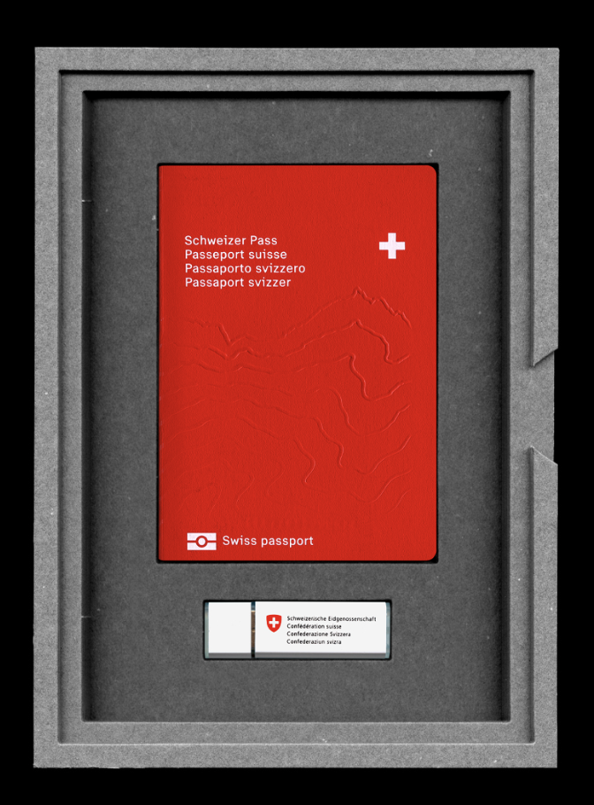
process/references/20231116_RefBox03.png
