qtxs/head-md-future-of-drawing/process/references/20231116_RefBox04.png

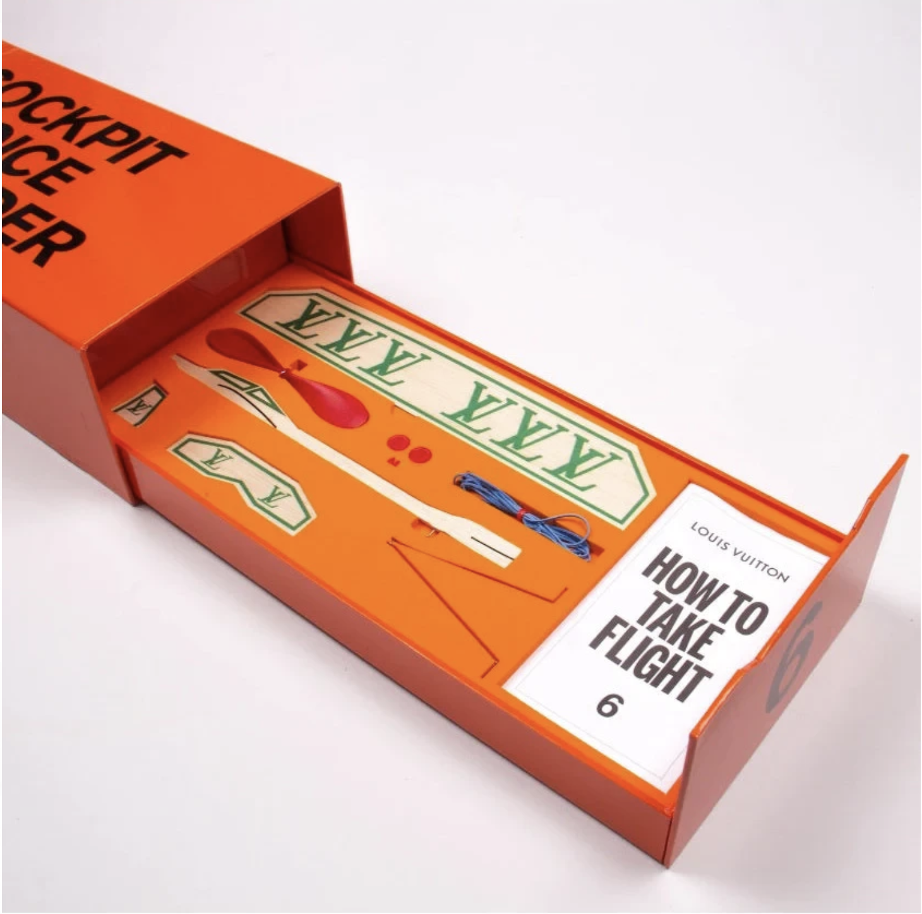
process/references/20231116_RefBox04.png
