qtxs/head-md-future-of-drawing/process/references/20231116_RefBox05.png

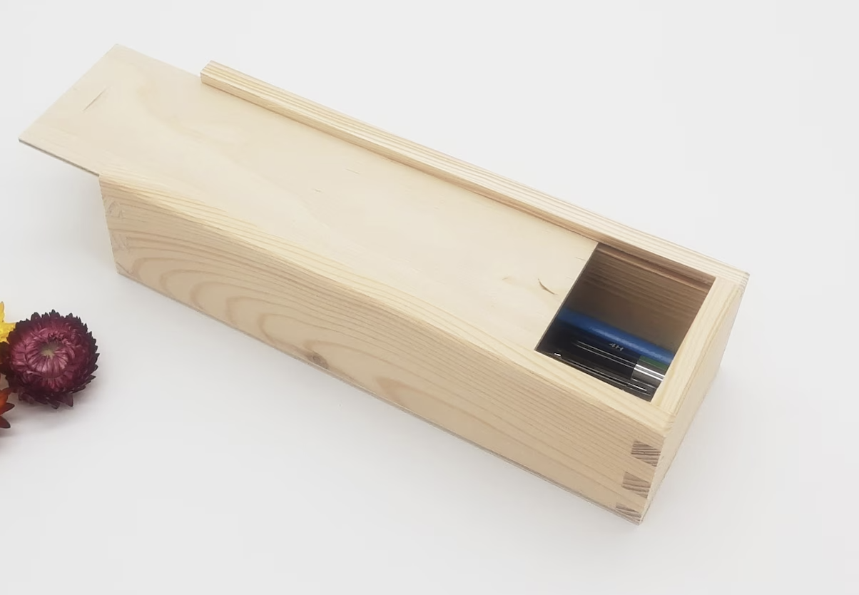
process/references/20231116_RefBox05.png
