qtxs/head-md-future-of-drawing/process/references/concrete_poetry_4.jpg

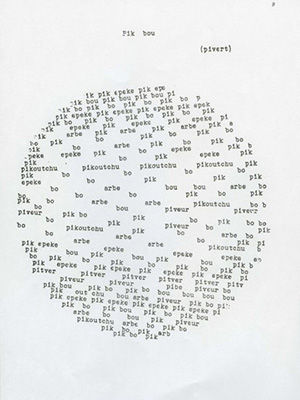
process/references/concrete_poetry_4.jpg
