qtxs/head-md-future-of-drawing/process/references/draper_target.jpg

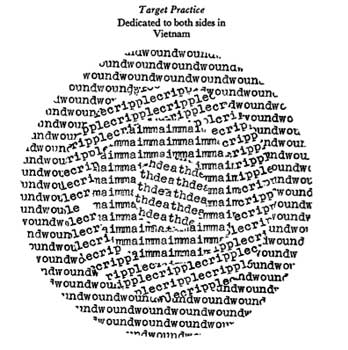
process/references/draper_target.jpg
