qtxs/head-md-future-of-drawing/process/references/Screenshot 2023-10-20 at 10.15.31.png

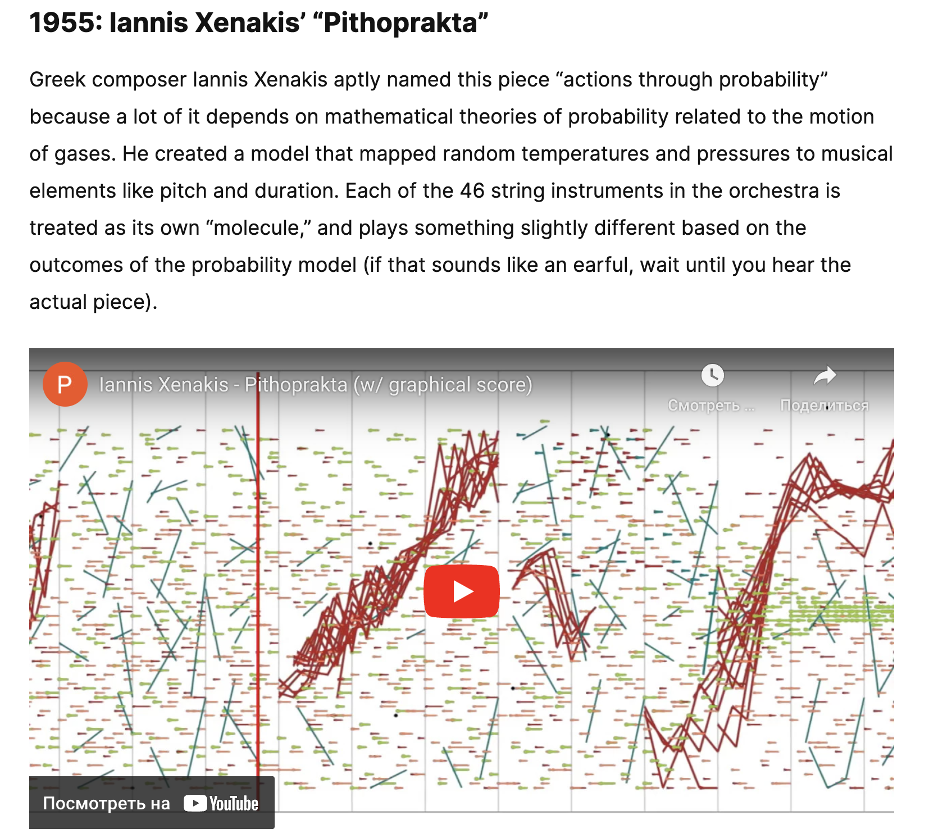
process/references/Screenshot 2023-10-20 at 10.15.31.png
