qtxs/head-md-future-of-drawing/process/references/Screenshot 2023-10-29 at 19.42.20.png

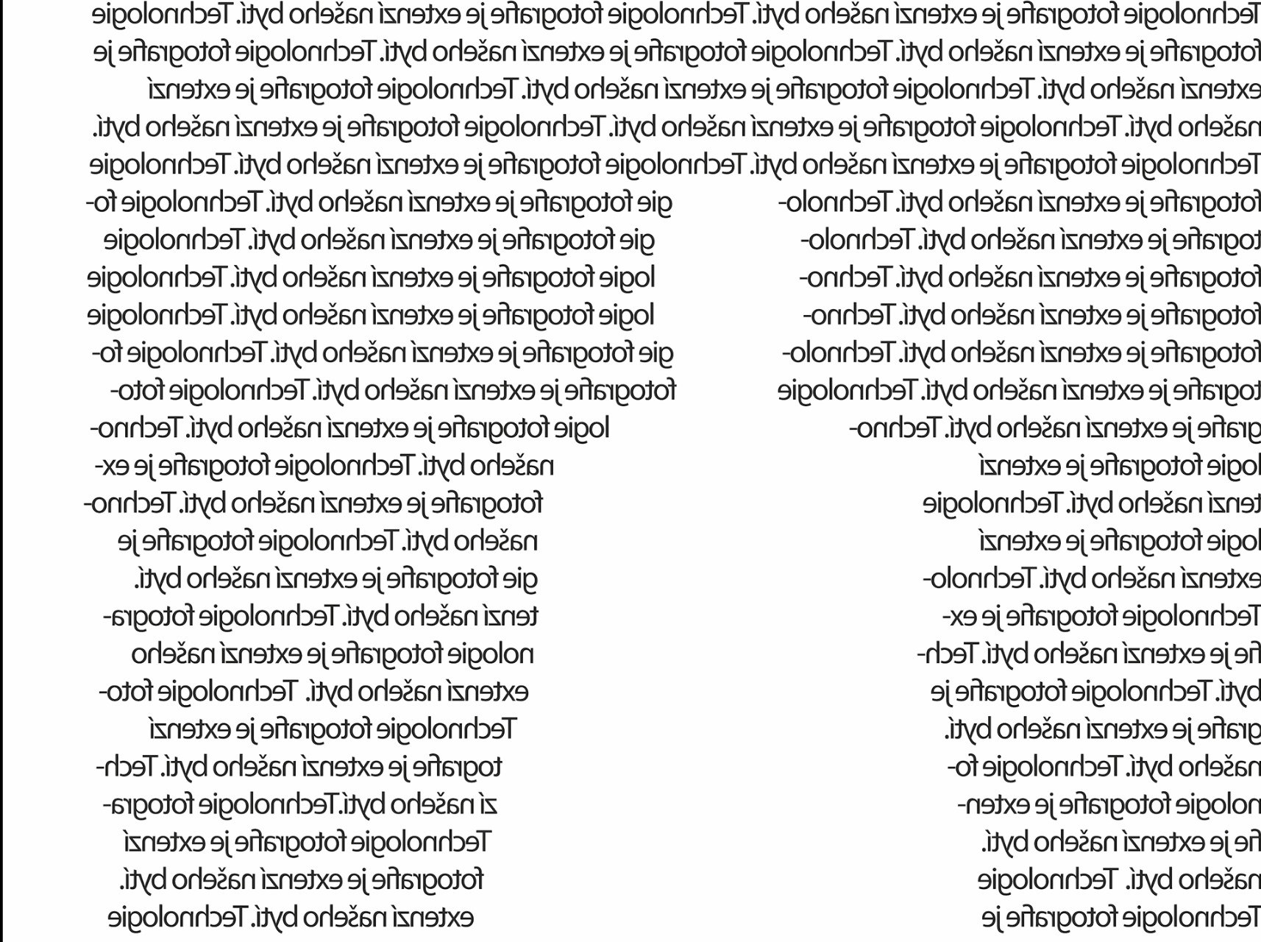
process/references/Screenshot 2023-10-29 at 19.42.20.png
