qtxs/head-md-future-of-drawing/process/references/Screenshot 2023-10-29 at 20.31.41.png

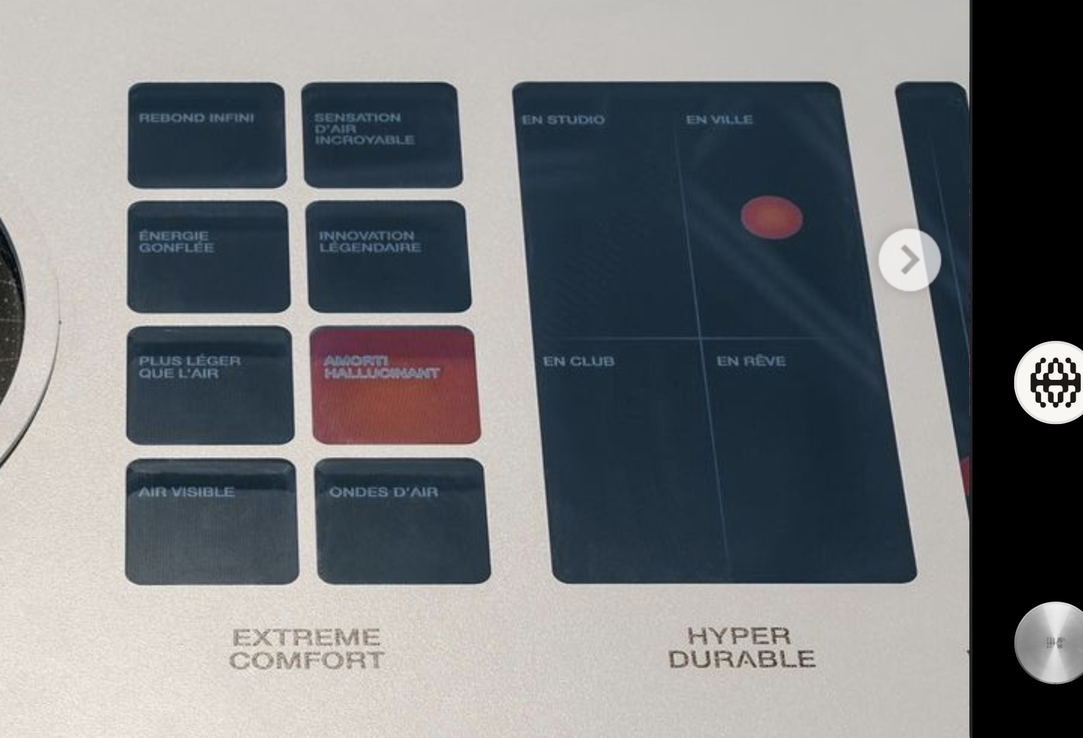
process/references/Screenshot 2023-10-29 at 20.31.41.png
