qtxs/head-md-future-of-drawing/process/references/Screenshot 2023-10-29 at 20.41.32.png

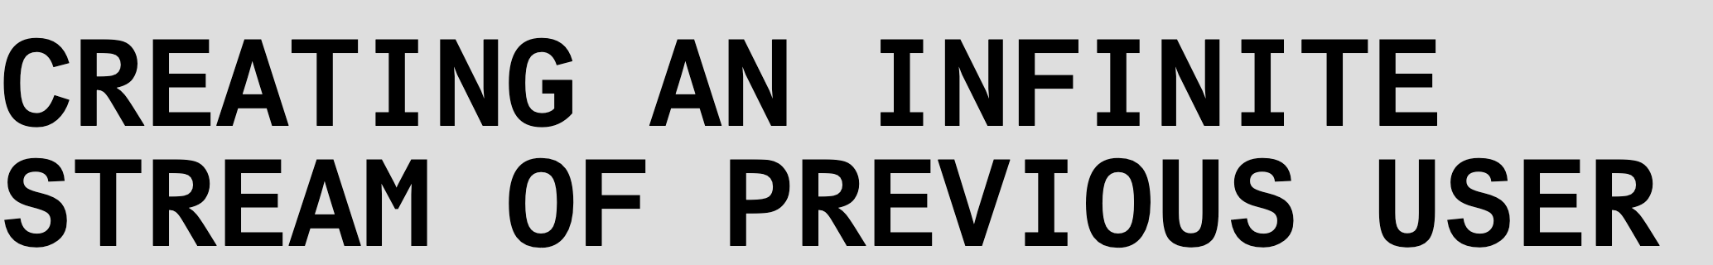
process/references/Screenshot 2023-10-29 at 20.41.32.png
