qtxs/head-md-future-of-drawing/process/references/Screenshot 2023-10-30 at 13.02.49.png

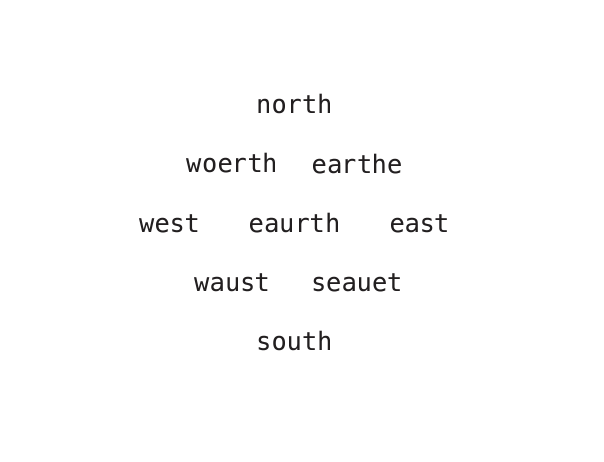
process/references/Screenshot 2023-10-30 at 13.02.49.png
