qtxs/head-md-future-of-drawing/process/references/Screenshot 2023-10-31 at 09.43.07.png

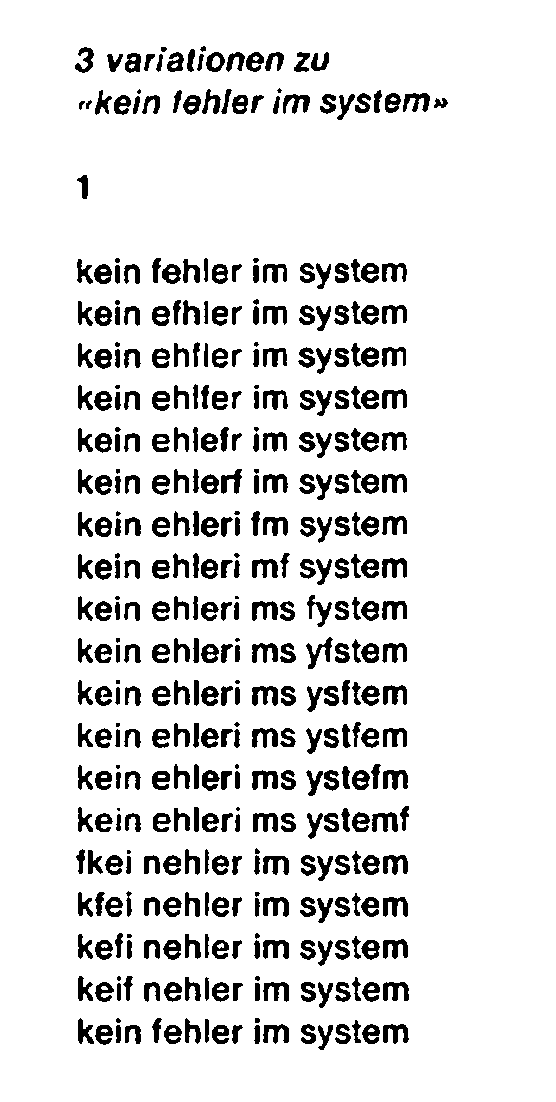
process/references/Screenshot 2023-10-31 at 09.43.07.png
