qtxs/head-md-future-of-drawing/process/references/Screenshot 2023-10-31 at 10.18.29.png

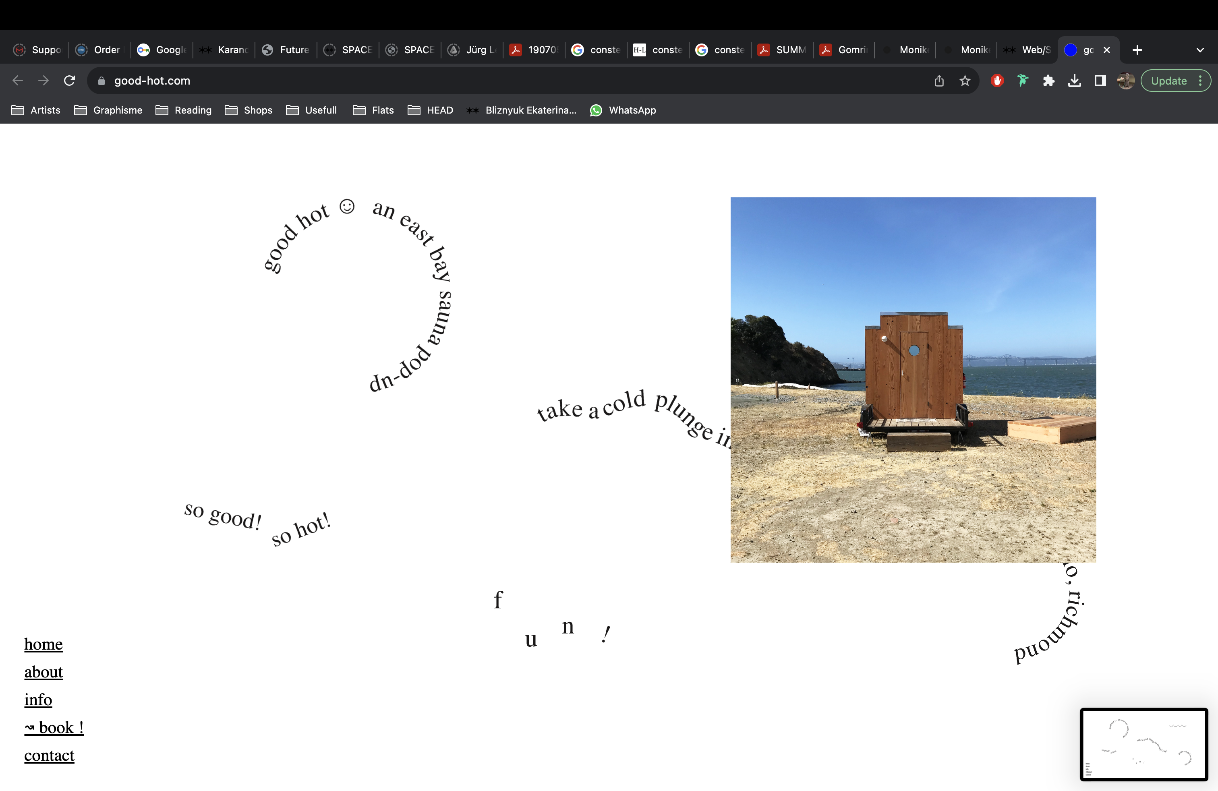
process/references/Screenshot 2023-10-31 at 10.18.29.png
