qtxs/head-md-future-of-drawing/process/references/Screenshot 2023-11-14 at 11.23.43.png

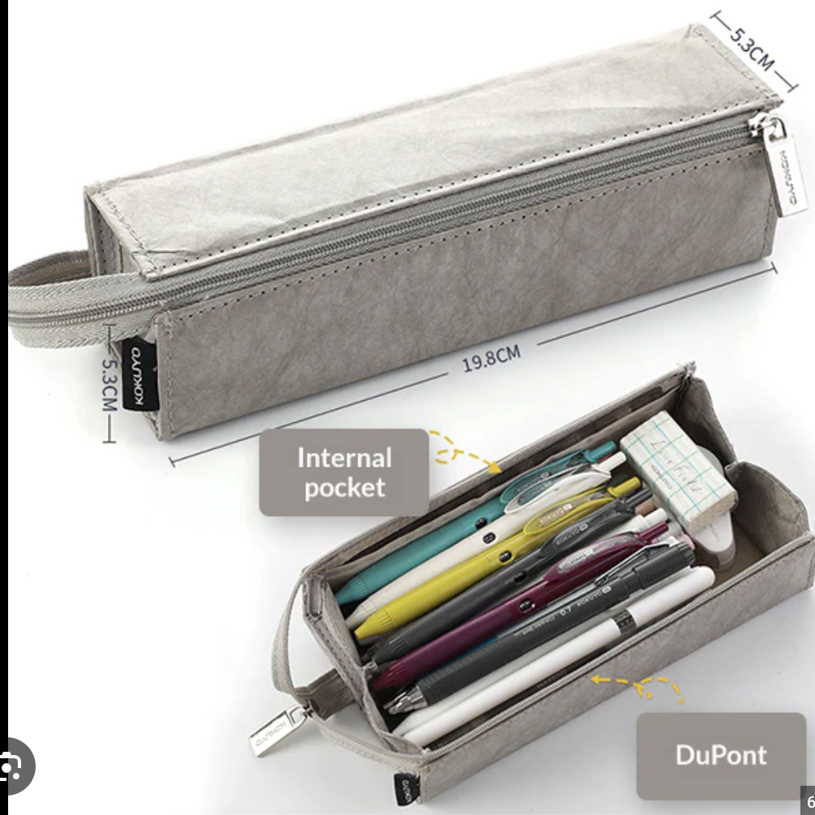
process/references/Screenshot 2023-11-14 at 11.23.43.png
