qtxs/head-md-future-of-drawing/process/references/Screenshot 2023-11-14 at 11.30.51.png

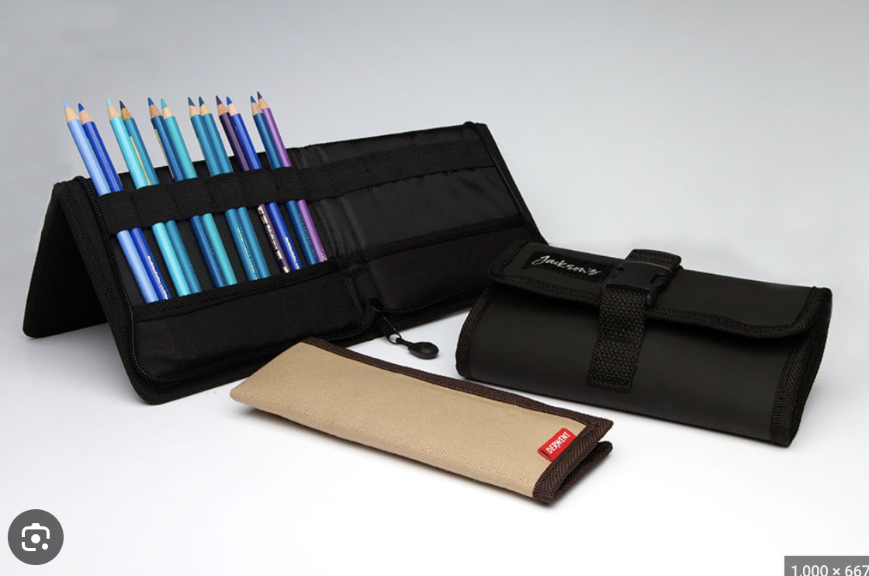
process/references/Screenshot 2023-11-14 at 11.30.51.png
