qtxs/head-md-future-of-drawing/process/references/Screenshot 2023-11-14 at 18.51.18.png

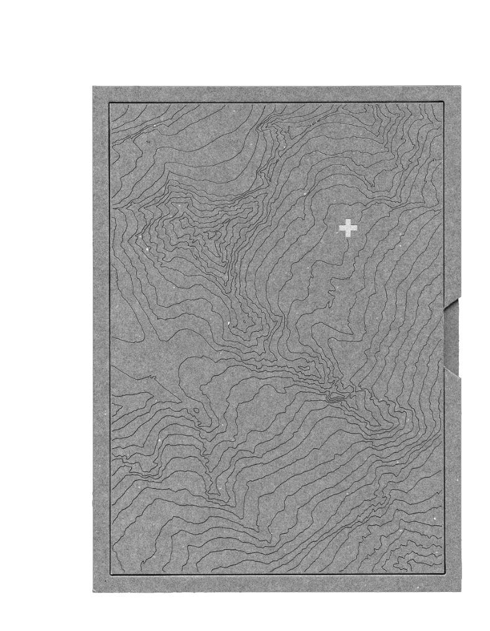
process/references/Screenshot 2023-11-14 at 18.51.18.png
