qtxs/head-md-future-of-drawing/process/references/Screenshot 2023-11-15 at 10.28.37.png

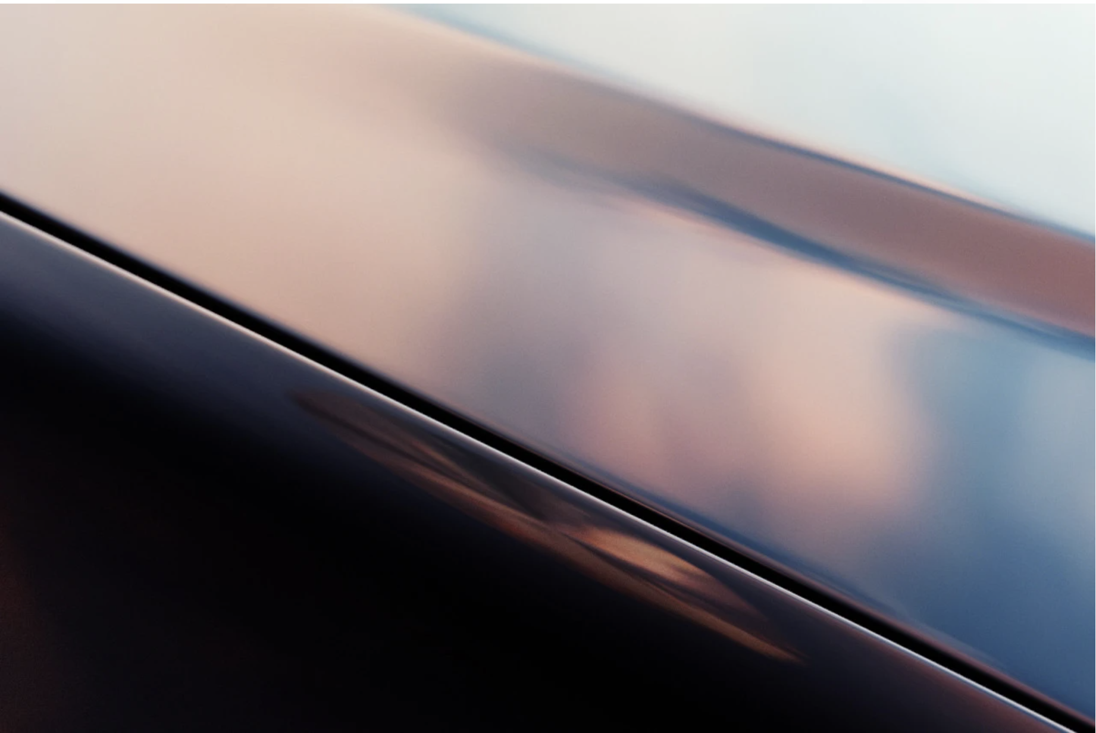
process/references/Screenshot 2023-11-15 at 10.28.37.png
