qtxs/head-md-future-of-drawing/process/references/Screenshot 2023-11-15 at 21.44.04.png

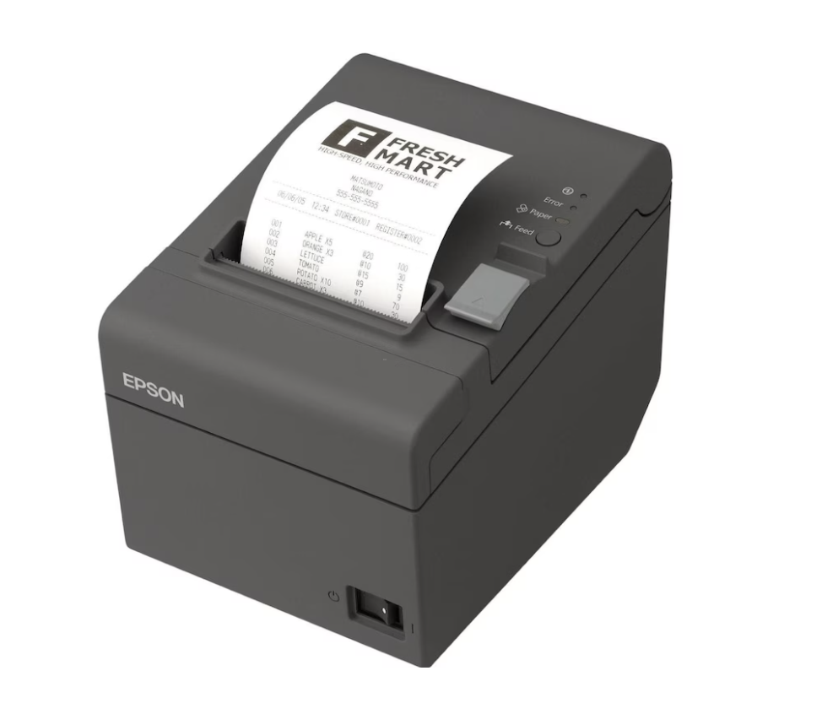
process/references/Screenshot 2023-11-15 at 21.44.04.png
