qtxs/head-md-future-of-drawing/process/references/Screenshot 2023-11-15 at 21.46.36.png

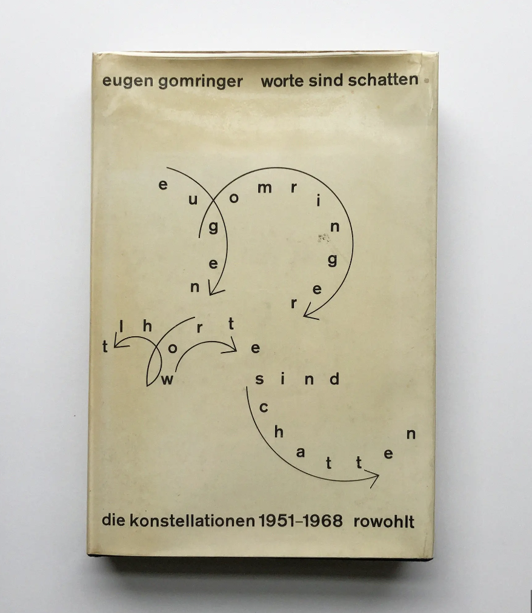
process/references/Screenshot 2023-11-15 at 21.46.36.png
