qtxs/head-md-future-of-drawing/process/references/Screenshot 2023-12-04 at 11.32.27.png

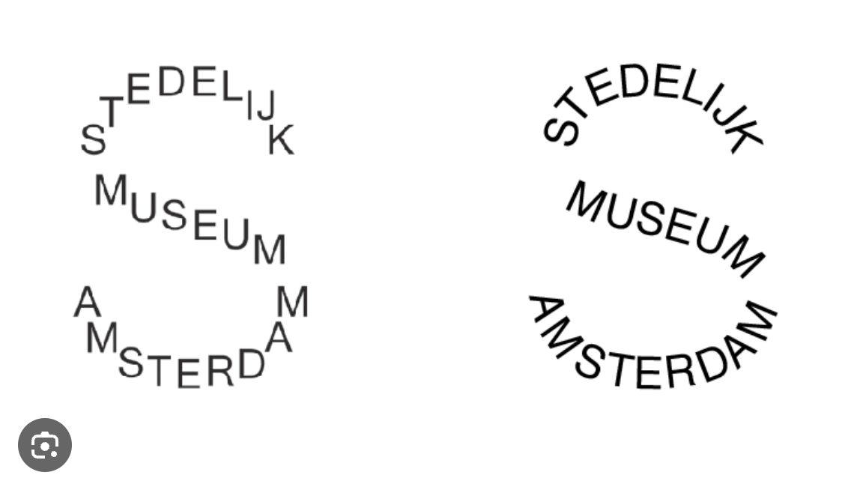
process/references/Screenshot 2023-12-04 at 11.32.27.png
