qtxs/head-md-future-of-drawing/process/references/Screenshot 2023-12-13 at 11.13.06.png

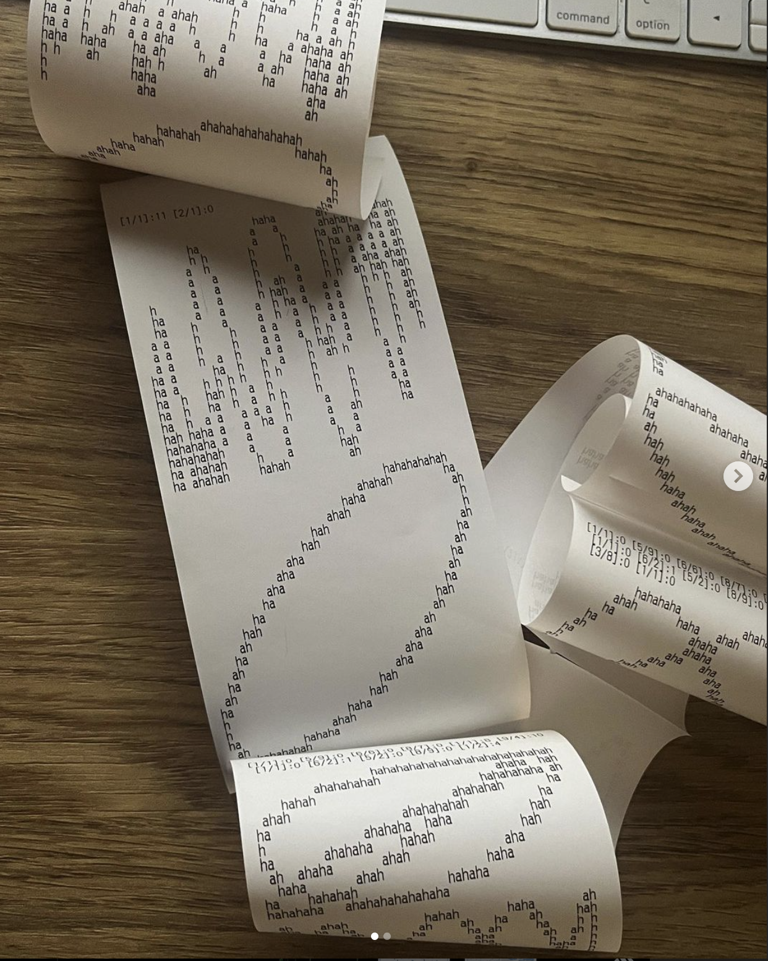
process/references/Screenshot 2023-12-13 at 11.13.06.png
