qtxs/head-md-future-of-drawing/process/references/Screenshot 2023-12-13 at 11.13.24.png

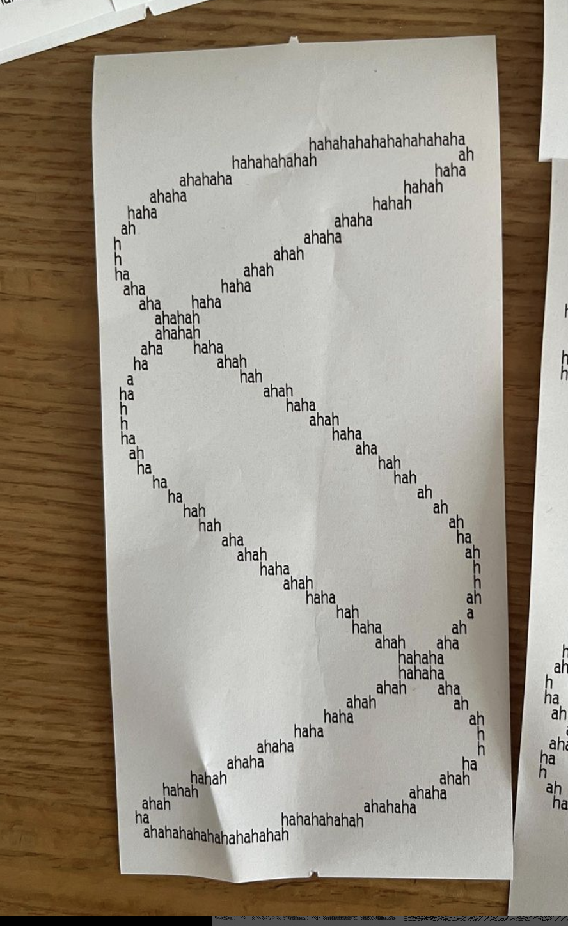
process/references/Screenshot 2023-12-13 at 11.13.24.png
