qtxs/head-md-future-of-drawing/process/references/Screenshot 2024-01-16 at 19.50.01.png

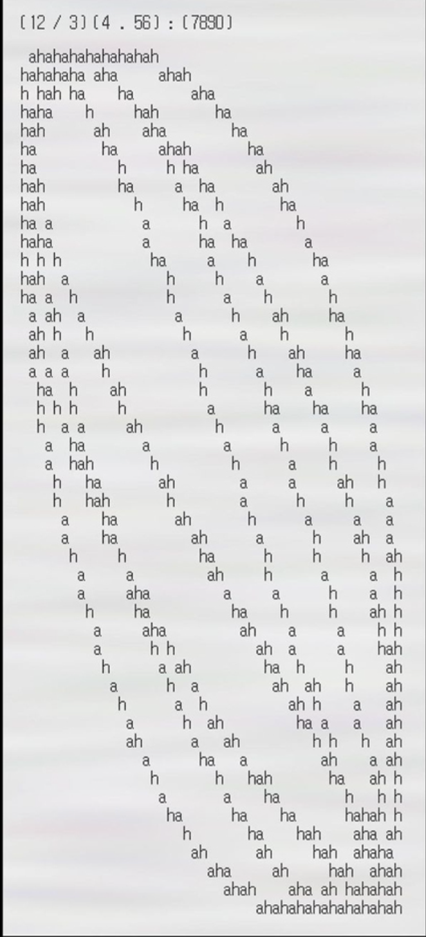
process/references/Screenshot 2024-01-16 at 19.50.01.png
