qtxs/head-md-future-of-drawing/process/main/2024-01-05/20241205_Print1.jpeg

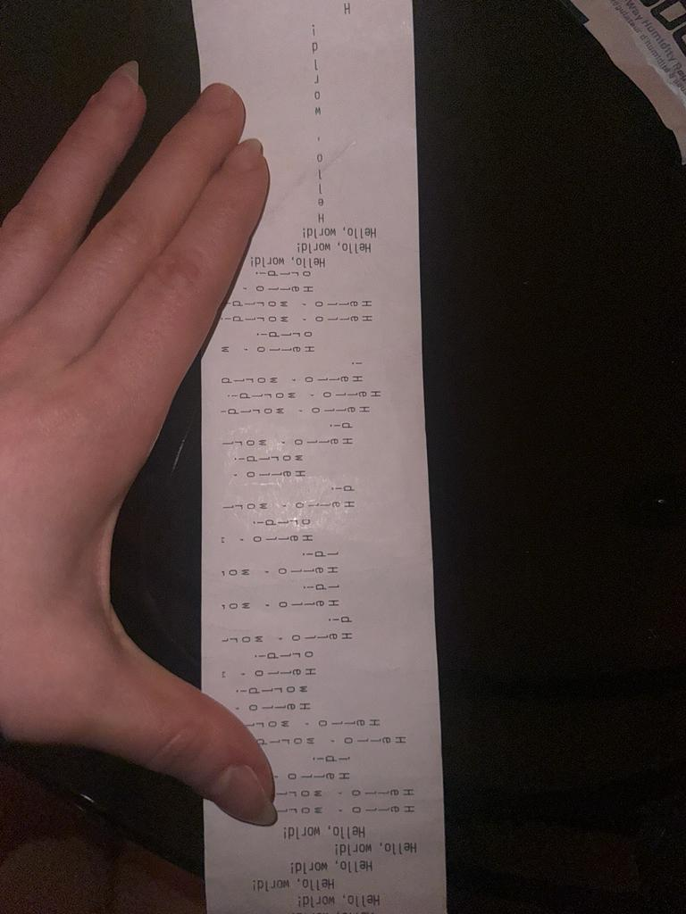
process/main/2024-01-05/20241205_Print1.jpeg
