qtxs/head-md-future-of-drawing/process/main/2024-01-08/20241208_Print2.JPG

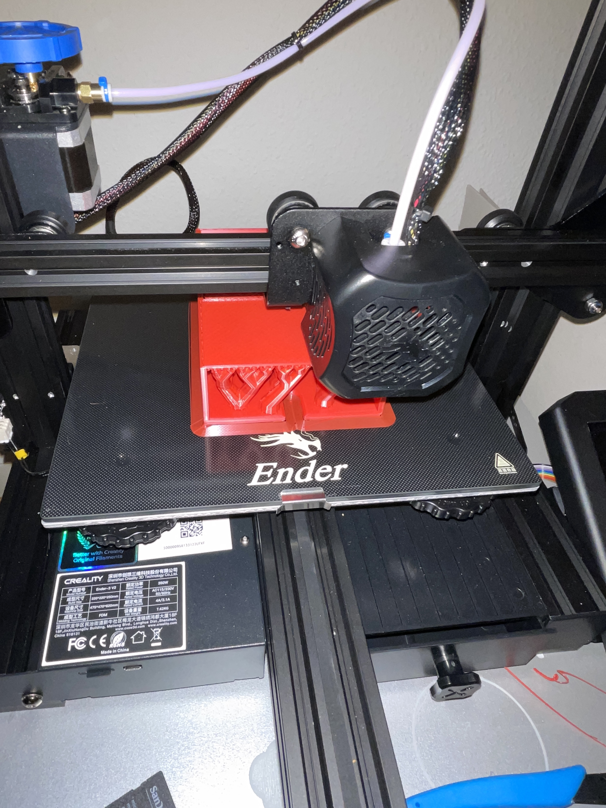
process/main/2024-01-08/20241208_Print2.JPG
