qtxs/head-md-future-of-drawing/process/main/2024-01-15/20240115_Print3.jpeg

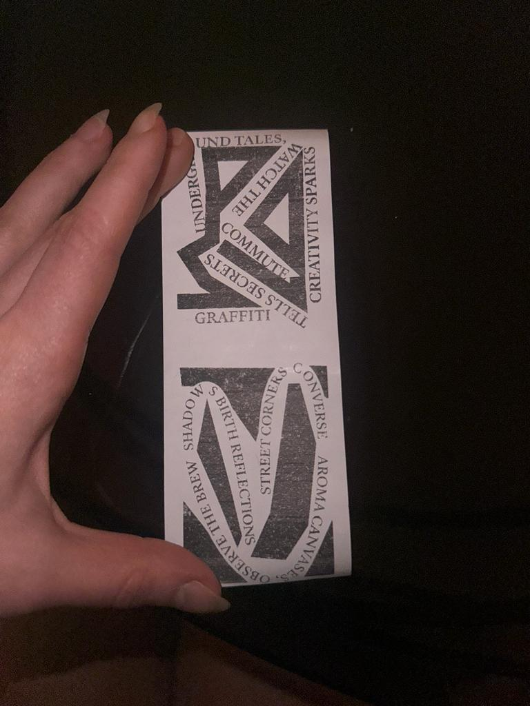
process/main/2024-01-15/20240115_Print3.jpeg
