qtxs/head-md-future-of-drawing/process/field-research/2023-10-30/raw/test-01-results_2023-10-20-09-01-20.jpeg

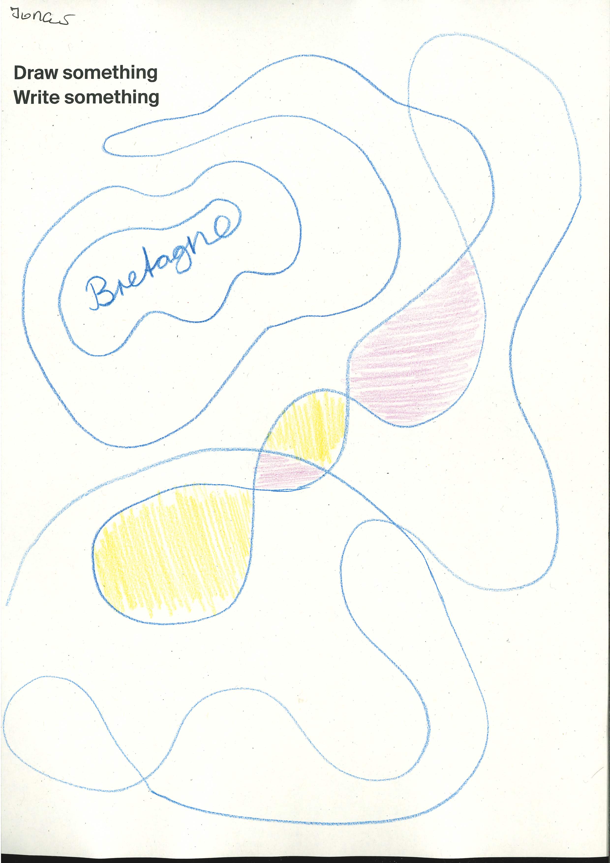
process/field-research/2023-10-30/raw/test-01-results_2023-10-20-09-01-20.jpeg
