qtxs/head-md-future-of-drawing/process/field-research/2023-11-02/test-01/IMG_6757.JPG

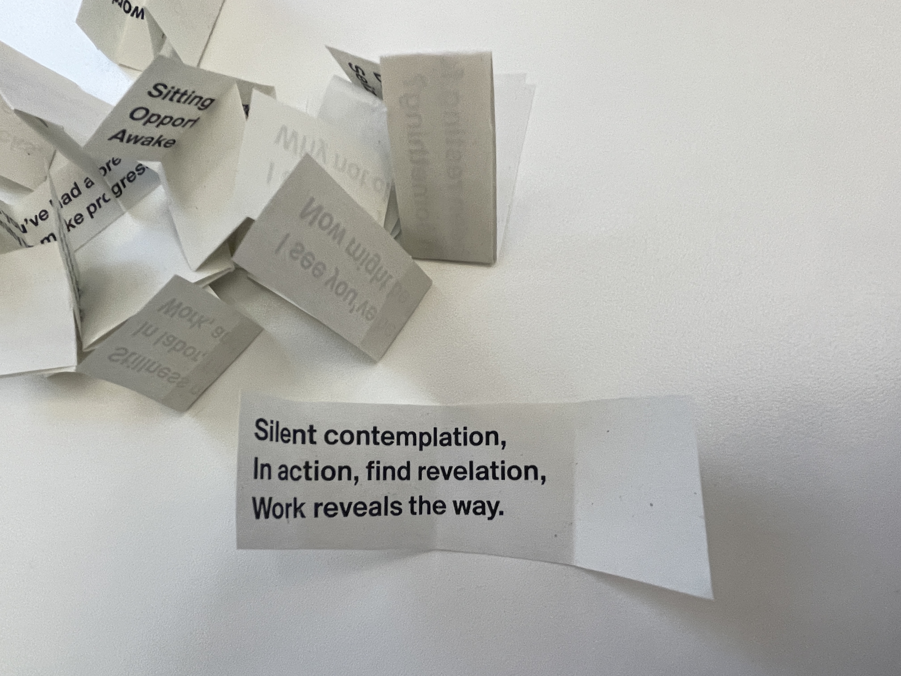
process/field-research/2023-11-02/test-01/IMG_6757.JPG
