qtxs/head-md-future-of-drawing/process/field-research/2023-11-02/test-02/IMG_6753.JPG

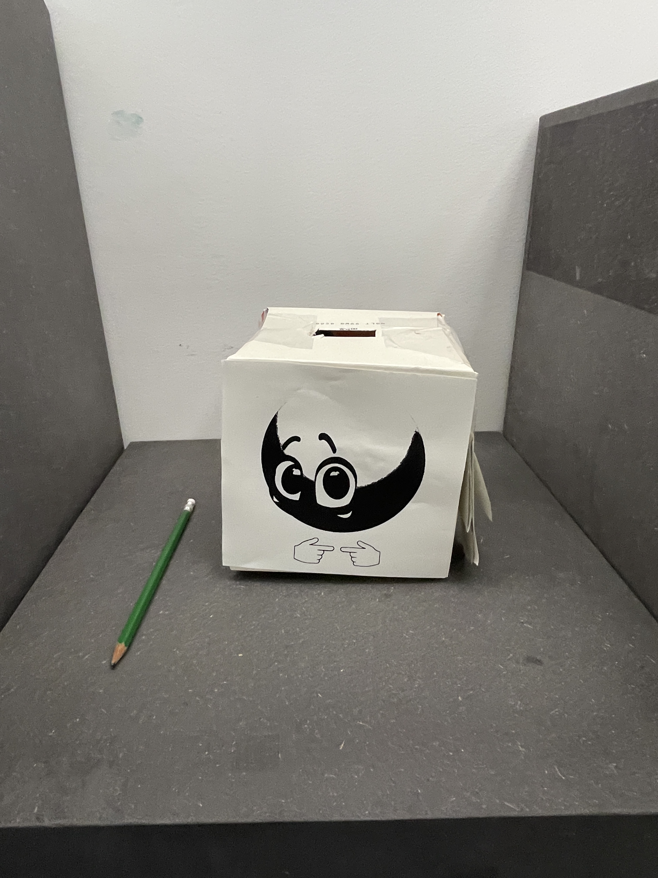
process/field-research/2023-11-02/test-02/IMG_6753.JPG
