qtxs/head-md-future-of-drawing/process/main/2023-12-14/TestDayPics/IMG_7495.JPG

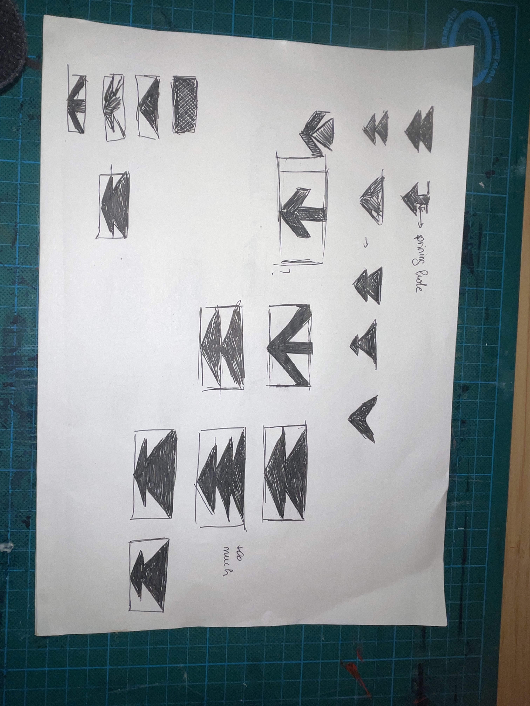
process/main/2023-12-14/TestDayPics/IMG_7495.JPG
