qtxs/head-md-future-of-drawing/process/main/2024-01-11/20241211_Polishing.JPG

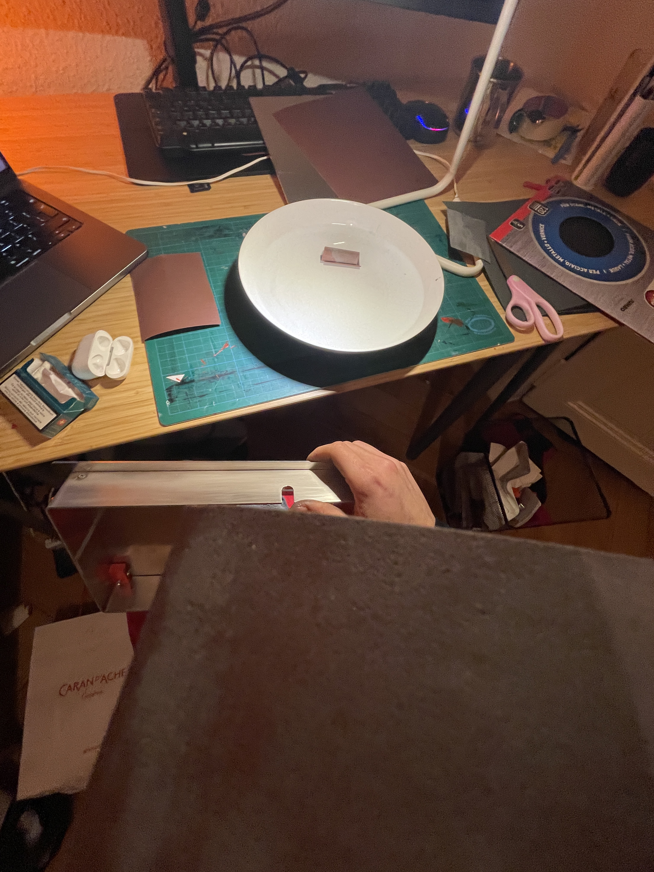
process/main/2024-01-11/20241211_Polishing.JPG
